matanbright/8BitComputer/pcb-files/8-Bit_Computer/8-Bit_Computer.kicad_sch

## KiCad design pcb-files/8-Bit_Computer/8-Bit_Computer.kicad_sch (2024-03-10)

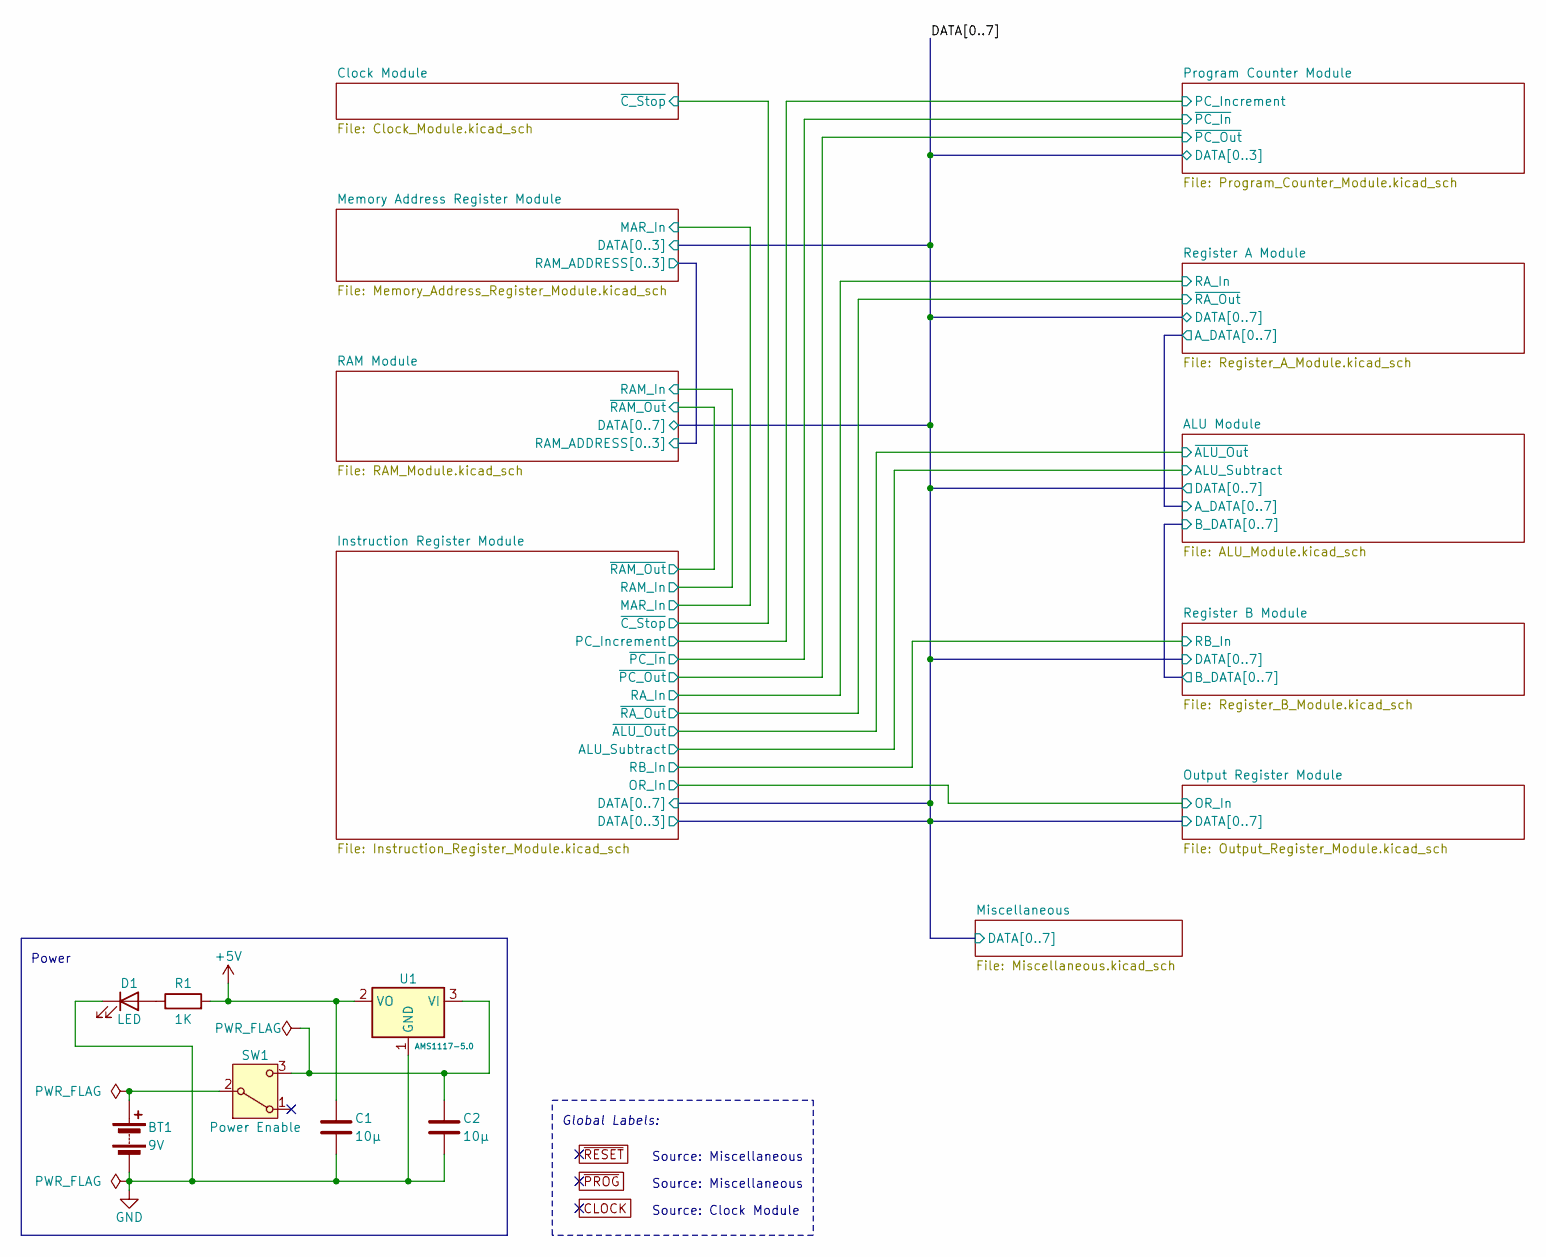
[picture p2: schematic 8-Bit_Computer.kicad_sch]

Parts:
BT1: 9V; BatteryHolder_Eagle_12BH611-GR
C1, C2: 10µ; C_Radial_D4.0mm_H7.0mm_P1.50mm
D1: LED; LED_D3.0mm
R1: 1K; R_Axial_DIN0207_L6.3mm_D2.5mm_P7.62mm_Horizontal
SW1: Power Enable; SW_SPDT
U1: AMS1117-5.0; SOT-223-3_TabPin2

Connections:
+5V: C1.1, R1.2, U1.2 (VO)
GND: BT1.2 (-), C1.2, C2.2, D1.1 (K), U1.1 (GND)
unnamed: BT1.1 (+), SW1.2 (B)
unnamed: C2.1, SW1.3 (C), U1.3 (VI)
unnamed: D1.2 (A), R1.1

Notes on the sheet:
Source: Clock Module
Power
Source: Miscellaneous
Global Labels:
