matanbright/8BitComputer/pcb-files/8-Bit_Computer/ALU_Module.kicad_sch

## KiCad design pcb-files/8-Bit_Computer/ALU_Module.kicad_sch (2024-03-10)

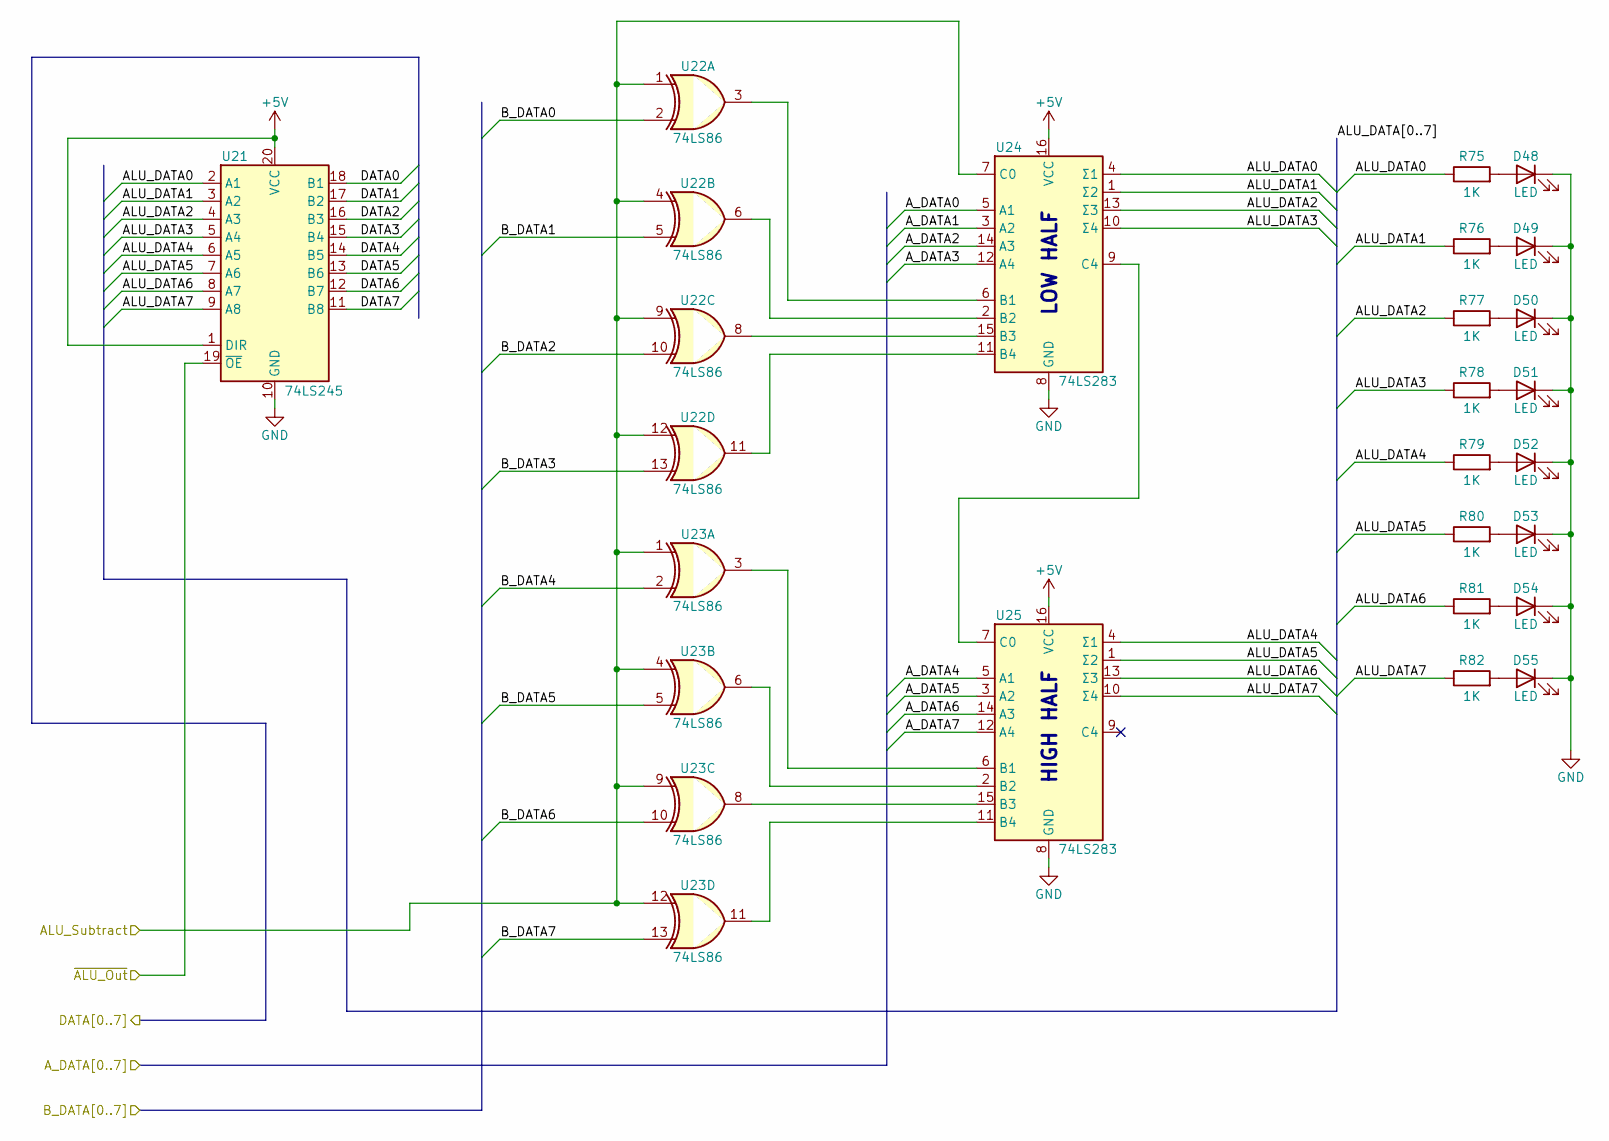
[picture p3: schematic ALU_Module.kicad_sch]

Parts:
D48, D49, D50, D51, D52, D53, D54, D55: LED; LED_D3.0mm
R75, R76, R77, R78, R79, R80, R81, R82: 1K; R_Axial_DIN0207_L6.3mm_D2.5mm_P7.62mm_Horizontal
U21: 74LS245; DIP-20_W7.62mm
U22, U23: 74LS86; DIP-14_W7.62mm
U24, U25: 74LS283; DIP-16_W7.62mm

Connections:
+5V: U21.1 (DIR), U21.20 (VCC), U24.16 (VCC), U25.16 (VCC)
ALU_DATA0: R75.1, U21.2 (A1), U24.4 (Σ1)
ALU_DATA1: R76.1, U21.3 (A2), U24.1 (Σ2)
ALU_DATA2: R77.1, U21.4 (A3), U24.13 (Σ3)
ALU_DATA3: R78.1, U21.5 (A4), U24.10 (Σ4)
ALU_DATA4: R79.1, U21.6 (A5), U25.4 (Σ1)
ALU_DATA5: R80.1, U21.7 (A6), U25.1 (Σ2)
ALU_DATA6: R81.1, U21.8 (A7), U25.13 (Σ3)
ALU_DATA7: R82.1, U21.9 (A8), U25.10 (Σ4)
ALU_Subtract: U22.1, U22.4, U22.9, U22.12, U23.1, U23.4, U23.9, U23.12, U24.7 (C0)
A_DATA0: U24.5 (A1)
A_DATA1: U24.3 (A2)
A_DATA2: U24.14 (A3)
A_DATA3: U24.12 (A4)
A_DATA4: U25.5 (A1)
A_DATA5: U25.3 (A2)
A_DATA6: U25.14 (A3)
A_DATA7: U25.12 (A4)
B_DATA0: U22.2
B_DATA1: U22.5
B_DATA2: U22.10
B_DATA3: U22.13
B_DATA4: U23.2
B_DATA5: U23.5
B_DATA6: U23.10
B_DATA7: U23.13
DATA0: U21.18 (B1)
DATA1: U21.17 (B2)
DATA2: U21.16 (B3)
DATA3: U21.15 (B4)
DATA4: U21.14 (B5)
DATA5: U21.13 (B6)
DATA6: U21.12 (B7)
DATA7: U21.11 (B8)
GND: D48.1 (K), D49.1 (K), D50.1 (K), D51.1 (K), D52.1 (K), D53.1 (K), D54.1 (K), D55.1 (K), U21.10 (GND), U24.8 (GND), U25.8 (GND)
unnamed: D48.2 (A), R75.2
unnamed: D49.2 (A), R76.2
unnamed: D50.2 (A), R77.2
unnamed: D51.2 (A), R78.2
unnamed: D52.2 (A), R79.2
unnamed: D53.2 (A), R80.2
unnamed: D54.2 (A), R81.2
unnamed: D55.2 (A), R82.2
unnamed: U22.3, U24.6 (B1)
unnamed: U22.6, U24.2 (B2)
unnamed: U22.8, U24.15 (B3)
unnamed: U22.11, U24.11 (B4)
unnamed: U23.3, U25.6 (B1)
unnamed: U23.6, U25.2 (B2)
unnamed: U23.8, U25.15 (B3)
unnamed: U23.11, U25.11 (B4)
unnamed: U24.9 (C4), U25.7 (C0)
~ALU_Out: U21.19 (~OE)

Notes on the sheet:
LOW HALF
HIGH HALF
