matanbright/8BitComputer/pcb-files/8-Bit_Computer/Clock_Module.kicad_sch

## KiCad design pcb-files/8-Bit_Computer/Clock_Module.kicad_sch (2024-03-10)

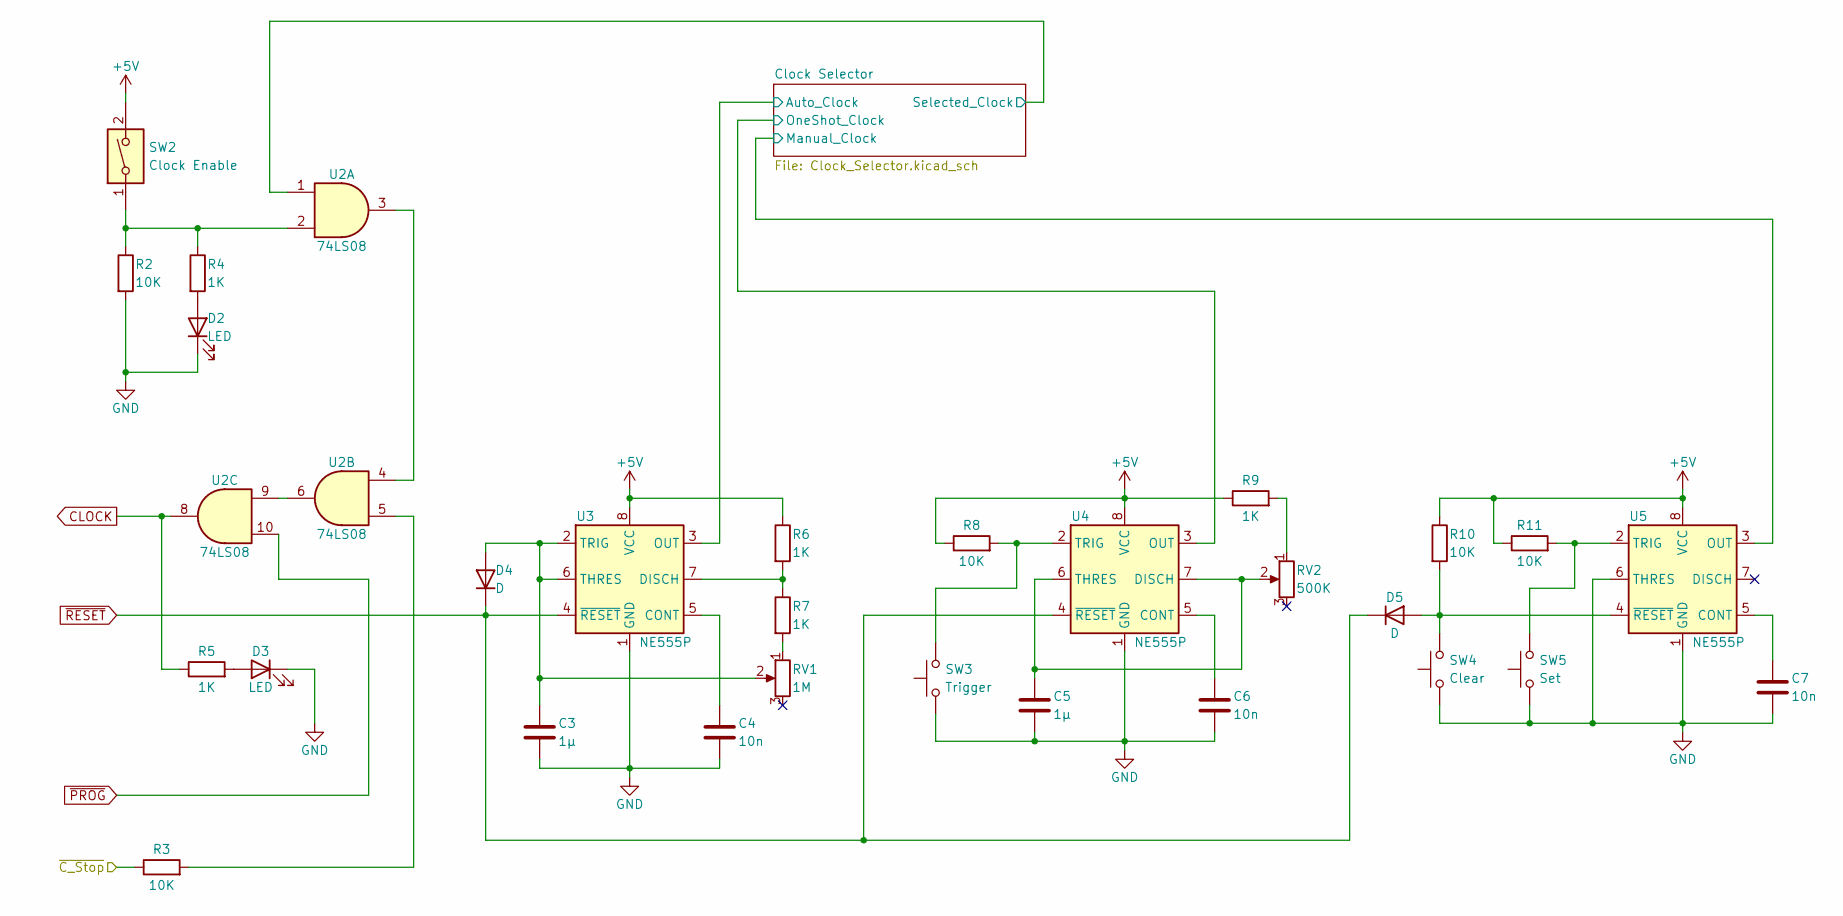
[picture p4: schematic Clock_Module.kicad_sch]

Parts:
C3, C5: 1µ; C_Disc_D5.1mm_W3.2mm_P5.00mm
C4, C6, C7: 10n; C_Disc_D5.1mm_W3.2mm_P5.00mm
D2, D3: LED; LED_D3.0mm
D4, D5: D; D_DO-34_SOD68_P7.62mm_Horizontal
R2, R3, R8, R10, R11: 10K; R_Axial_DIN0207_L6.3mm_D2.5mm_P7.62mm_Horizontal
R4, R5, R6, R7, R9: 1K; R_Axial_DIN0207_L6.3mm_D2.5mm_P7.62mm_Horizontal
RV1: 1M; Potentiometer_Vishay_T73YP_Vertical
RV2: 500K; Potentiometer_Vishay_T73YP_Vertical
SW2: Clock Enable; SW_DIP_SPSTx01_Slide_9.78x4.72mm_W7.62mm_P2.54mm
SW3: Trigger; SW_PUSH_6mm_H5mm
SW4: Clear; SW_PUSH_6mm_H5mm
SW5: Set; SW_PUSH_6mm_H5mm
U2: 74LS08; DIP-14_W7.62mm
U3, U4, U5: NE555P; DIP-8_W7.62mm

Connections:
+5V: R6.1, R8.1, R9.1, R10.1, R11.1, SW2.2, U3.8 (VCC), U4.8 (VCC), U5.8 (VCC)
Auto_Clock: U3.3 (OUT)
CLOCK: R5.1, U2.8
GND: C3.2, C4.2, C5.2, C6.2, C7.2, D2.1 (K), D3.1 (K), R2.2, SW3.1, SW4.1, SW5.1, U3.1 (GND), U4.1 (GND), U5.1 (GND), U5.6 (THRES)
Manual_Clock: U5.3 (OUT)
unnamed: C3.1, D4.2 (A), RV1.2, U3.2 (TRIG), U3.6 (THRES)
unnamed: C4.1, U3.5 (CONT)
unnamed: C5.1, RV2.2, U4.6 (THRES), U4.7 (DISCH)
unnamed: C6.1, U4.5 (CONT)
unnamed: C7.1, U5.5 (CONT)
unnamed: D2.2 (A), R4.2
unnamed: D3.2 (A), R5.2
unnamed: D5.2 (A), R10.2, SW4.2, U5.4 (~RESET)
unnamed: R2.1, R4.1, SW2.1, U2.2
unnamed: R3.2, U2.5
unnamed: R6.2, R7.1, U3.7 (DISCH)
unnamed: R7.2, RV1.1
unnamed: R8.2, SW3.2, U4.2 (TRIG)
unnamed: R9.2, RV2.1
unnamed: R11.2, SW5.2, U5.2 (TRIG)
unnamed: U2.3, U2.4
unnamed: U2.6, U2.9
OneShot_Clock: U4.3 (OUT)
Selected_Clock: U2.1
~C_Stop: R3.1
~PROG: U2.10
~RESET: D4.1 (K), D5.1 (K), U3.4 (~RESET), U4.4 (~RESET)
