matanbright/8BitComputer/pcb-files/8-Bit_Computer/Clock_Selector.kicad_sch

## KiCad design pcb-files/8-Bit_Computer/Clock_Selector.kicad_sch (2024-03-10)

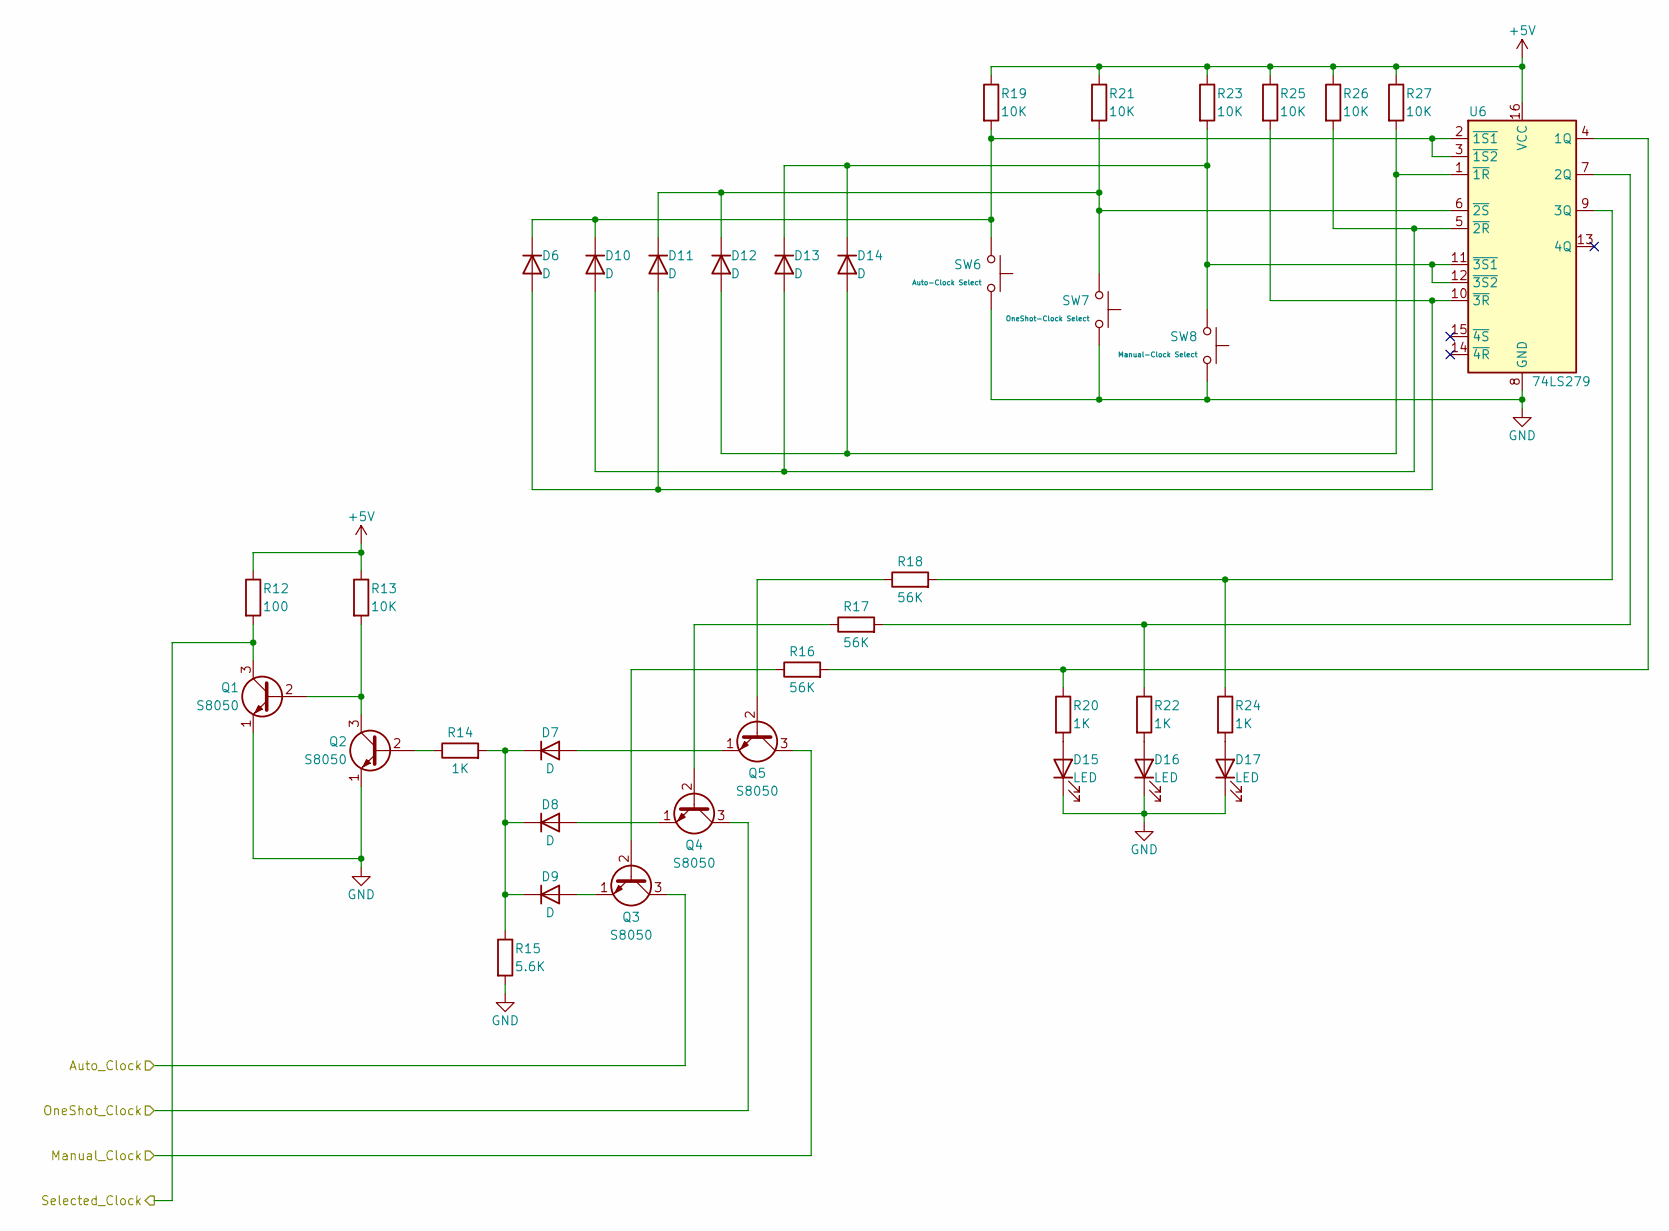
[picture p5: schematic Clock_Selector.kicad_sch]

Parts:
D6, D7, D8, D9, D10, D11, D12, D13, D14: D; D_DO-34_SOD68_P7.62mm_Horizontal
D15, D16, D17: LED; LED_D3.0mm
Q1, Q2, Q3, Q4, Q5: S8050; TO-92_Inline
R12: 100; R_Axial_DIN0207_L6.3mm_D2.5mm_P7.62mm_Horizontal
R13, R19, R21, R23, R25, R26, R27: 10K; R_Axial_DIN0207_L6.3mm_D2.5mm_P7.62mm_Horizontal
R14, R20, R22, R24: 1K; R_Axial_DIN0207_L6.3mm_D2.5mm_P7.62mm_Horizontal
R15: 5.6K; R_Axial_DIN0207_L6.3mm_D2.5mm_P7.62mm_Horizontal
R16, R17, R18: 56K; R_Axial_DIN0207_L6.3mm_D2.5mm_P7.62mm_Horizontal
SW6: Auto-Clock Select; SW_PUSH_6mm_H5mm
SW7: OneShot-Clock Select; SW_PUSH_6mm_H5mm
SW8: Manual-Clock Select; SW_PUSH_6mm_H5mm
U6: 74LS279; DIP-16_W7.62mm

Connections:
+5V: R12.1, R13.1, R19.1, R21.1, R23.1, R25.1, R26.1, R27.1, U6.16 (VCC)
Auto_Clock: Q3.3 (C)
GND: D15.1 (K), D16.1 (K), D17.1 (K), Q1.1 (E), Q2.1 (E), R15.2, SW6.1, SW7.1, SW8.1, U6.8 (GND)
Manual_Clock: Q5.3 (C)
unnamed: D7.1 (K), D8.1 (K), D9.1 (K), R14.2, R15.1
unnamed: D7.2 (A), Q5.1 (E)
unnamed: D8.2 (A), Q4.1 (E)
unnamed: D9.2 (A), Q3.1 (E)
unnamed: D6.1 (K), D10.1 (K), R19.2, SW6.2, U6.2 (~1S1), U6.3 (~1S2)
unnamed: D10.2 (A), D13.2 (A), R26.2, U6.5 (~2R)
unnamed: D11.1 (K), D12.1 (K), R21.2, SW7.2, U6.6 (~2S)
unnamed: D6.2 (A), D11.2 (A), R25.2, U6.10 (~3R)
unnamed: D12.2 (A), D14.2 (A), R27.2, U6.1 (~1R)
unnamed: D13.1 (K), D14.1 (K), R23.2, SW8.2, U6.11 (~3S1), U6.12 (~3S2)
unnamed: D15.2 (A), R20.2
unnamed: D16.2 (A), R22.2
unnamed: D17.2 (A), R24.2
unnamed: Q1.2 (B), Q2.3 (C), R13.2
unnamed: Q2.2 (B), R14.1
unnamed: Q3.2 (B), R16.1
unnamed: Q4.2 (B), R17.1
unnamed: Q5.2 (B), R18.1
unnamed: R16.2, R20.1, U6.4 (1Q)
unnamed: R17.2, R22.1, U6.7 (2Q)
unnamed: R18.2, R24.1, U6.9 (3Q)
OneShot_Clock: Q4.3 (C)
Selected_Clock: Q1.3 (C), R12.2
