matanbright/8BitComputer/pcb-files/8-Bit_Computer/Instruction_Register_Module.kicad_sch

## KiCad design pcb-files/8-Bit_Computer/Instruction_Register_Module.kicad_sch (2024-03-10)

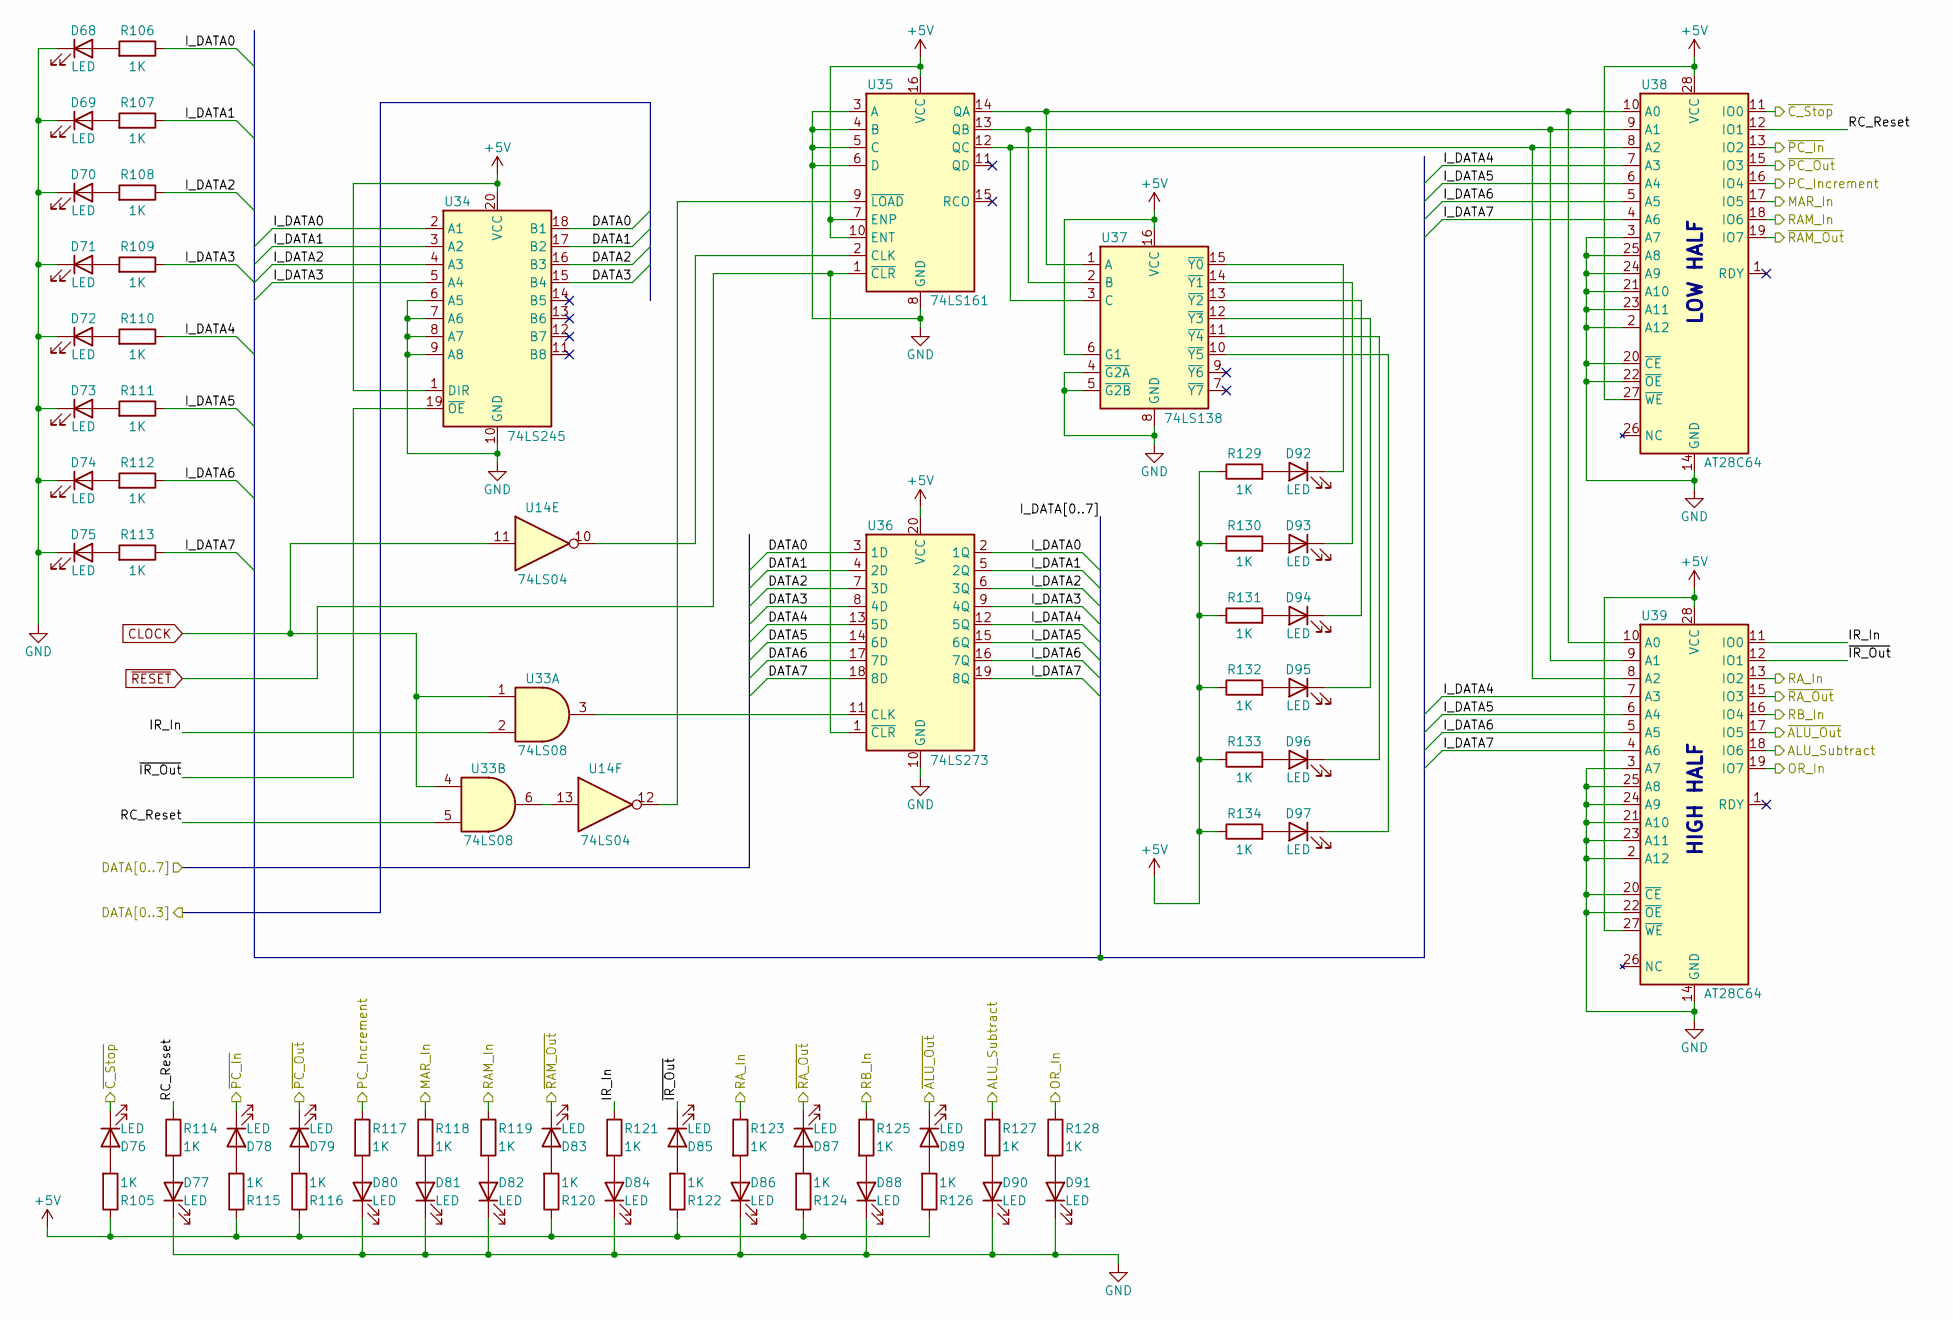
[picture p6: schematic Instruction_Register_Module.kicad_sch]

Parts:
D68, D69, D70, D71, D72, D73, D74, D75, D76, D77, D78, D79, D80, D81, D82, D83, D84, D85, D86, D87, D88, D89, D90, D91, D92, D93, D94, D95, D96, D97: LED; LED_D3.0mm
R105, R106, R107, R108, R109, R110, R111, R112, R113, R114, R115, R116, R117, R118, R119, R120, R121, R122, R123, R124, R125, R126, R127, R128, R129, R130, R131, R132, R133, R134: 1K; R_Axial_DIN0207_L6.3mm_D2.5mm_P7.62mm_Horizontal
U14: 74LS04; DIP-14_W7.62mm
U33: 74LS08; DIP-14_W7.62mm
U34: 74LS245; DIP-20_W7.62mm
U35: 74LS161; DIP-16_W7.62mm
U36: 74LS273; DIP-20_W7.62mm
U37: 74LS138; DIP-16_W7.62mm
U38, U39: AT28C64; DIP-28_W15.24mm

Connections:
+5V: R105.1, R115.1, R116.1, R120.1, R122.1, R124.1, R126.1, R129.1, R130.1, R131.1, R132.1, R133.1, R134.1, U34.1 (DIR), U34.20 (VCC), U35.7 (ENP), U35.10 (ENT), U35.16 (VCC), U36.20 (VCC), U37.6 (G1), U37.16 (VCC), U38.27 (~WE), U38.28 (VCC), U39.27 (~WE), U39.28 (VCC)
ALU_Subtract: R127.1, U39.18 (IO6)
CLOCK: U14.11, U33.1, U33.4
DATA0: U34.18 (B1), U36.3 (1D)
DATA1: U34.17 (B2), U36.4 (2D)
DATA2: U34.16 (B3), U36.7 (3D)
DATA3: U34.15 (B4), U36.8 (4D)
DATA4: U36.13 (5D)
DATA5: U36.14 (6D)
DATA6: U36.17 (7D)
DATA7: U36.18 (8D)
GND: D68.1 (K), D69.1 (K), D70.1 (K), D71.1 (K), D72.1 (K), D73.1 (K), D74.1 (K), D75.1 (K), D77.1 (K), D80.1 (K), D81.1 (K), D82.1 (K), D84.1 (K), D86.1 (K), D88.1 (K), D90.1 (K), D91.1 (K), U34.6 (A5), U34.7 (A6), U34.8 (A7), U34.9 (A8), U34.10 (GND), U35.3 (A), U35.4 (B), U35.5 (C), U35.6 (D), U35.8 (GND), U36.10 (GND), U37.4 (~G2A), U37.5 (~G2B), U37.8 (GND), U38.2 (A12), U38.3 (A7), U38.14 (GND), U38.20 (~CE), U38.21 (A10), U38.22 (~OE), U38.23 (A11), U38.24 (A9), U38.25 (A8), U39.2 (A12), U39.3 (A7), U39.14 (GND), U39.20 (~CE), U39.21 (A10), U39.22 (~OE), U39.23 (A11), U39.24 (A9), U39.25 (A8)
IR_In: R121.1, U33.2, U39.11 (IO0)
I_DATA0: R106.1, U34.2 (A1), U36.2 (1Q)
I_DATA1: R107.1, U34.3 (A2), U36.5 (2Q)
I_DATA2: R108.1, U34.4 (A3), U36.6 (3Q)
I_DATA3: R109.1, U34.5 (A4), U36.9 (4Q)
I_DATA4: R110.1, U36.12 (5Q), U38.7 (A3), U39.7 (A3)
I_DATA5: R111.1, U36.15 (6Q), U38.6 (A4), U39.6 (A4)
I_DATA6: R112.1, U36.16 (7Q), U38.5 (A5), U39.5 (A5)
I_DATA7: R113.1, U36.19 (8Q), U38.4 (A6), U39.4 (A6)
MAR_In: R118.1, U38.17 (IO5)
unnamed: D68.2 (A), R106.2
unnamed: D69.2 (A), R107.2
unnamed: D70.2 (A), R108.2
unnamed: D71.2 (A), R109.2
unnamed: D72.2 (A), R110.2
unnamed: D73.2 (A), R111.2
unnamed: D74.2 (A), R112.2
unnamed: D75.2 (A), R113.2
unnamed: D76.2 (A), R105.2
unnamed: D77.2 (A), R114.2
unnamed: D78.2 (A), R115.2
unnamed: D79.2 (A), R116.2
unnamed: D80.2 (A), R117.2
unnamed: D81.2 (A), R118.2
unnamed: D82.2 (A), R119.2
unnamed: D83.2 (A), R120.2
unnamed: D84.2 (A), R121.2
unnamed: D85.2 (A), R122.2
unnamed: D86.2 (A), R123.2
unnamed: D87.2 (A), R124.2
unnamed: D88.2 (A), R125.2
unnamed: D89.2 (A), R126.2
unnamed: D90.2 (A), R127.2
unnamed: D91.2 (A), R128.2
unnamed: D92.1 (K), U37.15 (~Y0)
unnamed: D92.2 (A), R129.2
unnamed: D93.1 (K), U37.14 (~Y1)
unnamed: D93.2 (A), R130.2
unnamed: D94.1 (K), U37.13 (~Y2)
unnamed: D94.2 (A), R131.2
unnamed: D95.1 (K), U37.12 (~Y3)
unnamed: D95.2 (A), R132.2
unnamed: D96.1 (K), U37.11 (~Y4)
unnamed: D96.2 (A), R133.2
unnamed: D97.1 (K), U37.10 (~Y5)
unnamed: D97.2 (A), R134.2
unnamed: U14.10, U35.2 (CLK)
unnamed: U14.12, U35.9 (~LOAD)
unnamed: U14.13, U33.6
unnamed: U33.3, U36.11 (CLK)
unnamed: U35.12 (QC), U37.3 (C), U38.8 (A2), U39.8 (A2)
unnamed: U35.13 (QB), U37.2 (B), U38.9 (A1), U39.9 (A1)
unnamed: U35.14 (QA), U37.1 (A), U38.10 (A0), U39.10 (A0)
OR_In: R128.1, U39.19 (IO7)
PC_Increment: R117.1, U38.16 (IO4)
RAM_In: R119.1, U38.18 (IO6)
RA_In: R123.1, U39.13 (IO2)
RB_In: R125.1, U39.16 (IO4)
RC_Reset: R114.1, U33.5, U38.12 (IO1)
~ALU_Out: D89.1 (K), U39.17 (IO5)
~C_Stop: D76.1 (K), U38.11 (IO0)
~IR_Out: D85.1 (K), U34.19 (~OE), U39.12 (IO1)
~PC_In: D78.1 (K), U38.13 (IO2)
~PC_Out: D79.1 (K), U38.15 (IO3)
~RAM_Out: D83.1 (K), U38.19 (IO7)
~RA_Out: D87.1 (K), U39.15 (IO3)
~RESET: U35.1 (~CLR), U36.1 (~CLR)

Notes on the sheet:
HIGH HALF
LOW HALF
