matanbright/8BitComputer/pcb-files/8-Bit_Computer/Memory_Address_Overrider.kicad_sch

## KiCad design pcb-files/8-Bit_Computer/Memory_Address_Overrider.kicad_sch (2024-03-10)

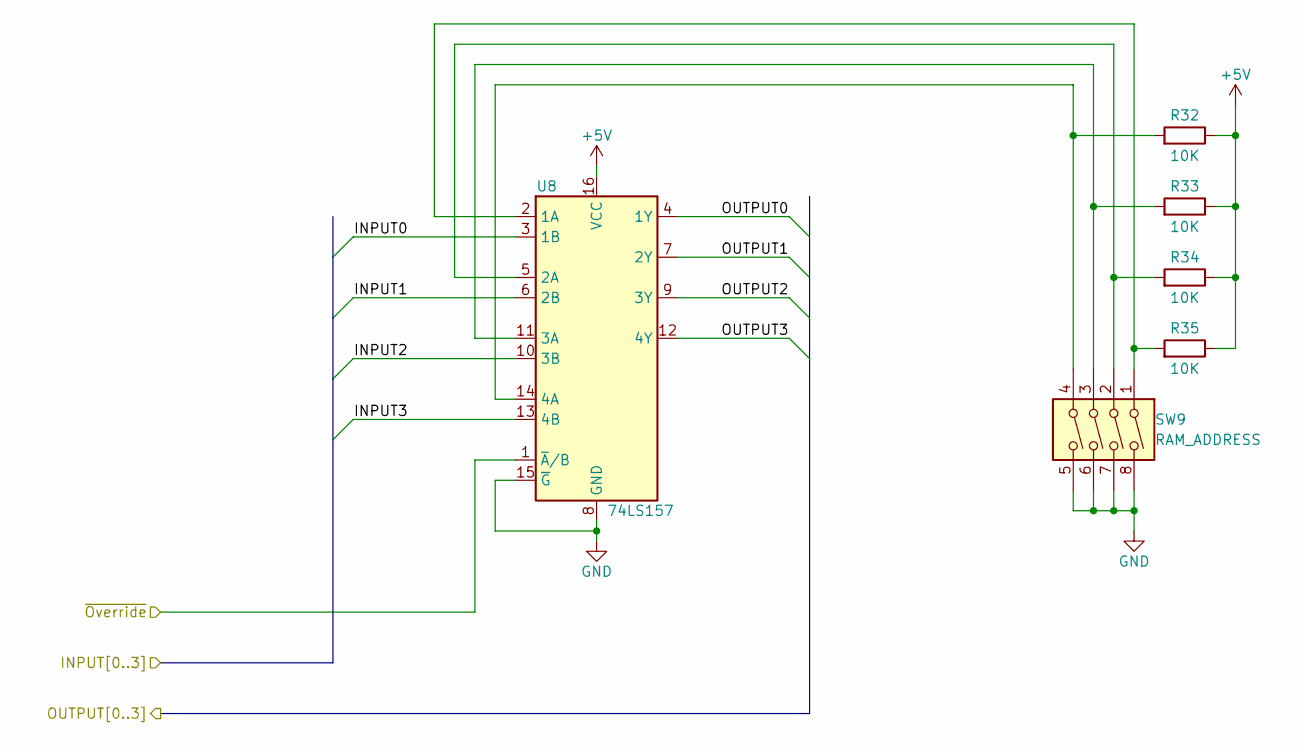
[picture p7: schematic Memory_Address_Overrider.kicad_sch]

Parts:
R32, R33, R34, R35: 10K; R_Axial_DIN0207_L6.3mm_D2.5mm_P7.62mm_Horizontal
SW9: RAM_ADDRESS; SW_DIP_SPSTx04_Slide_9.78x12.34mm_W7.62mm_P2.54mm
U8: 74LS157; DIP-16_W7.62mm

Connections:
+5V: R32.1, R33.1, R34.1, R35.1, U8.16 (VCC)
GND: SW9.5, SW9.6, SW9.7, SW9.8, U8.8 (GND), U8.15 (~G)
INPUT0: U8.3 (1B)
INPUT1: U8.6 (2B)
INPUT2: U8.10 (3B)
INPUT3: U8.13 (4B)
unnamed: R32.2, SW9.4, U8.14 (4A)
unnamed: R33.2, SW9.3, U8.11 (3A)
unnamed: R34.2, SW9.2, U8.5 (2A)
unnamed: R35.2, SW9.1, U8.2 (1A)
OUTPUT0: U8.4 (1Y)
OUTPUT1: U8.7 (2Y)
OUTPUT2: U8.9 (3Y)
OUTPUT3: U8.12 (4Y)
~Override: U8.1 (~A/B)
