matanbright/8BitComputer/pcb-files/8-Bit_Computer/Memory_Address_Register_Module.kicad_sch

## KiCad design pcb-files/8-Bit_Computer/Memory_Address_Register_Module.kicad_sch (2024-03-10)

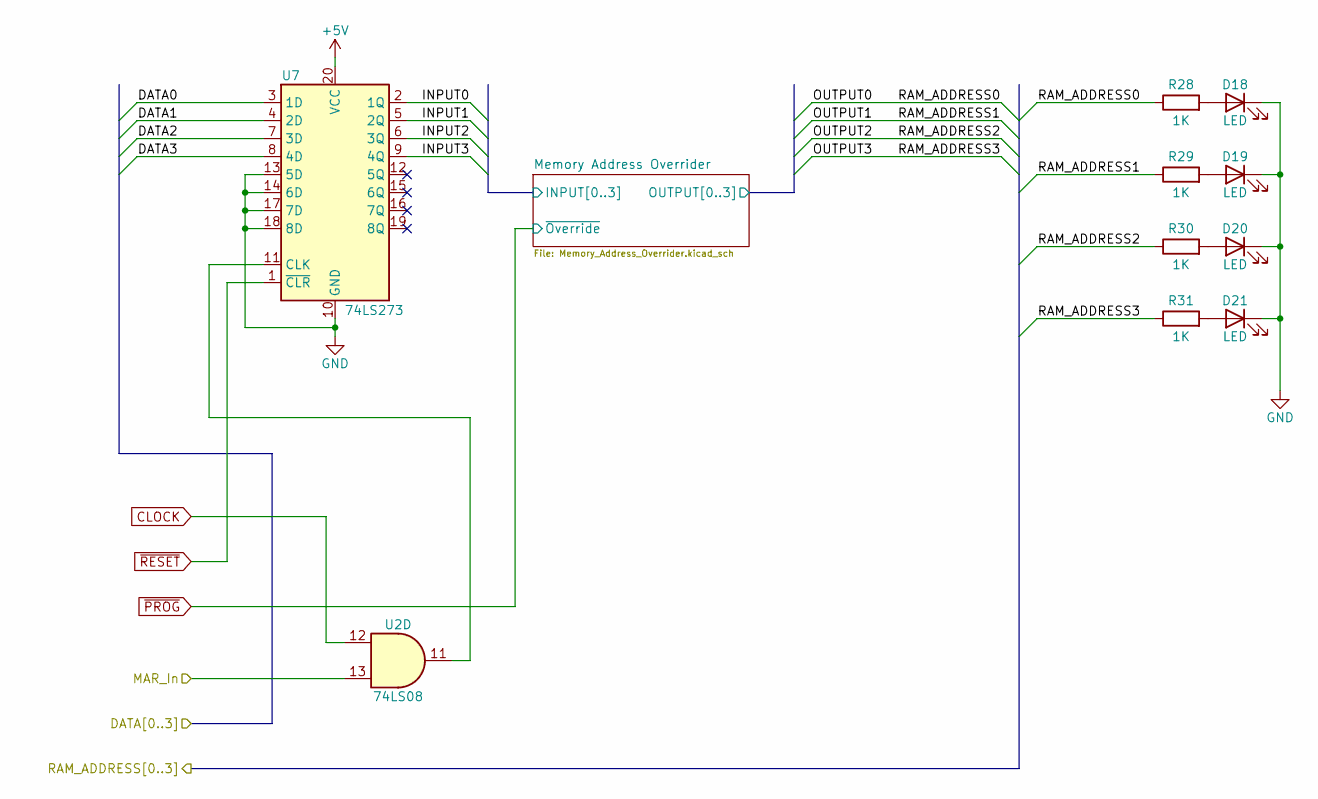
[picture p8: schematic Memory_Address_Register_Module.kicad_sch]

Parts:
D18, D19, D20, D21: LED; LED_D3.0mm
R28, R29, R30, R31: 1K; R_Axial_DIN0207_L6.3mm_D2.5mm_P7.62mm_Horizontal
U2: 74LS08; DIP-14_W7.62mm
U7: 74LS273; DIP-20_W7.62mm

Connections:
+5V: U7.20 (VCC)
CLOCK: U2.12
DATA0: U7.3 (1D)
DATA1: U7.4 (2D)
DATA2: U7.7 (3D)
DATA3: U7.8 (4D)
GND: D18.1 (K), D19.1 (K), D20.1 (K), D21.1 (K), U7.10 (GND), U7.13 (5D), U7.14 (6D), U7.17 (7D), U7.18 (8D)
INPUT0: U7.2 (1Q)
INPUT1: U7.5 (2Q)
INPUT2: U7.6 (3Q)
INPUT3: U7.9 (4Q)
MAR_In: U2.13
unnamed: D18.2 (A), R28.2
unnamed: D19.2 (A), R29.2
unnamed: D20.2 (A), R30.2
unnamed: D21.2 (A), R31.2
unnamed: U2.11, U7.11 (CLK)
OUTPUT0: R28.1
OUTPUT1: R29.1
OUTPUT2: R30.1
OUTPUT3: R31.1
~RESET: U7.1 (~CLR)
