matanbright/8BitComputer/pcb-files/8-Bit_Computer/Memory_Data_Overrider.kicad_sch

## KiCad design pcb-files/8-Bit_Computer/Memory_Data_Overrider.kicad_sch (2024-03-10)

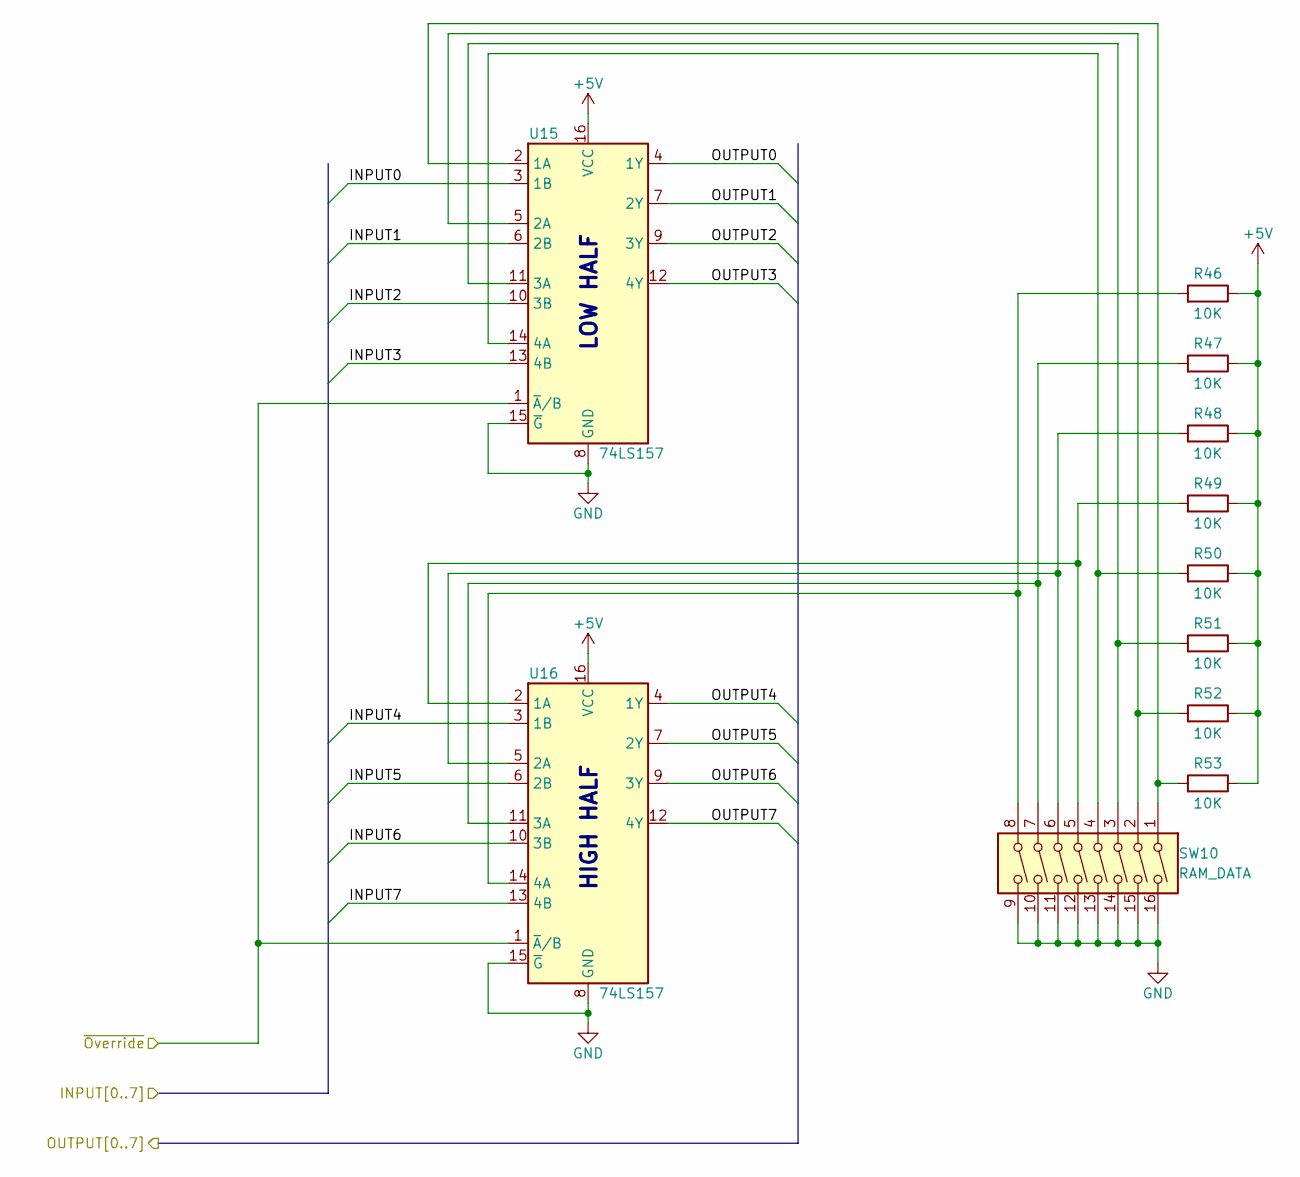
[picture p9: schematic Memory_Data_Overrider.kicad_sch]

Parts:
R46, R47, R48, R49, R50, R51, R52, R53: 10K; R_Axial_DIN0207_L6.3mm_D2.5mm_P7.62mm_Horizontal
SW10: RAM_DATA; SW_DIP_SPSTx08_Slide_9.78x22.5mm_W7.62mm_P2.54mm
U15, U16: 74LS157; DIP-16_W7.62mm

Connections:
+5V: R46.1, R47.1, R48.1, R49.1, R50.1, R51.1, R52.1, R53.1, U15.16 (VCC), U16.16 (VCC)
GND: SW10.9, SW10.10, SW10.11, SW10.12, SW10.13, SW10.14, SW10.15, SW10.16, U15.8 (GND), U15.15 (~G), U16.8 (GND), U16.15 (~G)
INPUT0: U15.3 (1B)
INPUT1: U15.6 (2B)
INPUT2: U15.10 (3B)
INPUT3: U15.13 (4B)
INPUT4: U16.3 (1B)
INPUT5: U16.6 (2B)
INPUT6: U16.10 (3B)
INPUT7: U16.13 (4B)
unnamed: R46.2, SW10.8, U16.14 (4A)
unnamed: R47.2, SW10.7, U16.11 (3A)
unnamed: R48.2, SW10.6, U16.5 (2A)
unnamed: R49.2, SW10.5, U16.2 (1A)
unnamed: R50.2, SW10.4, U15.14 (4A)
unnamed: R51.2, SW10.3, U15.11 (3A)
unnamed: R52.2, SW10.2, U15.5 (2A)
unnamed: R53.2, SW10.1, U15.2 (1A)
OUTPUT0: U15.4 (1Y)
OUTPUT1: U15.7 (2Y)
OUTPUT2: U15.9 (3Y)
OUTPUT3: U15.12 (4Y)
OUTPUT4: U16.4 (1Y)
OUTPUT5: U16.7 (2Y)
OUTPUT6: U16.9 (3Y)
OUTPUT7: U16.12 (4Y)
~Override: U15.1 (~A/B), U16.1 (~A/B)

Notes on the sheet:
LOW HALF
HIGH HALF
