matanbright/8BitComputer/pcb-files/8-Bit_Computer/Memory_Write_Overrider.kicad_sch

## KiCad design pcb-files/8-Bit_Computer/Memory_Write_Overrider.kicad_sch (2024-03-10)

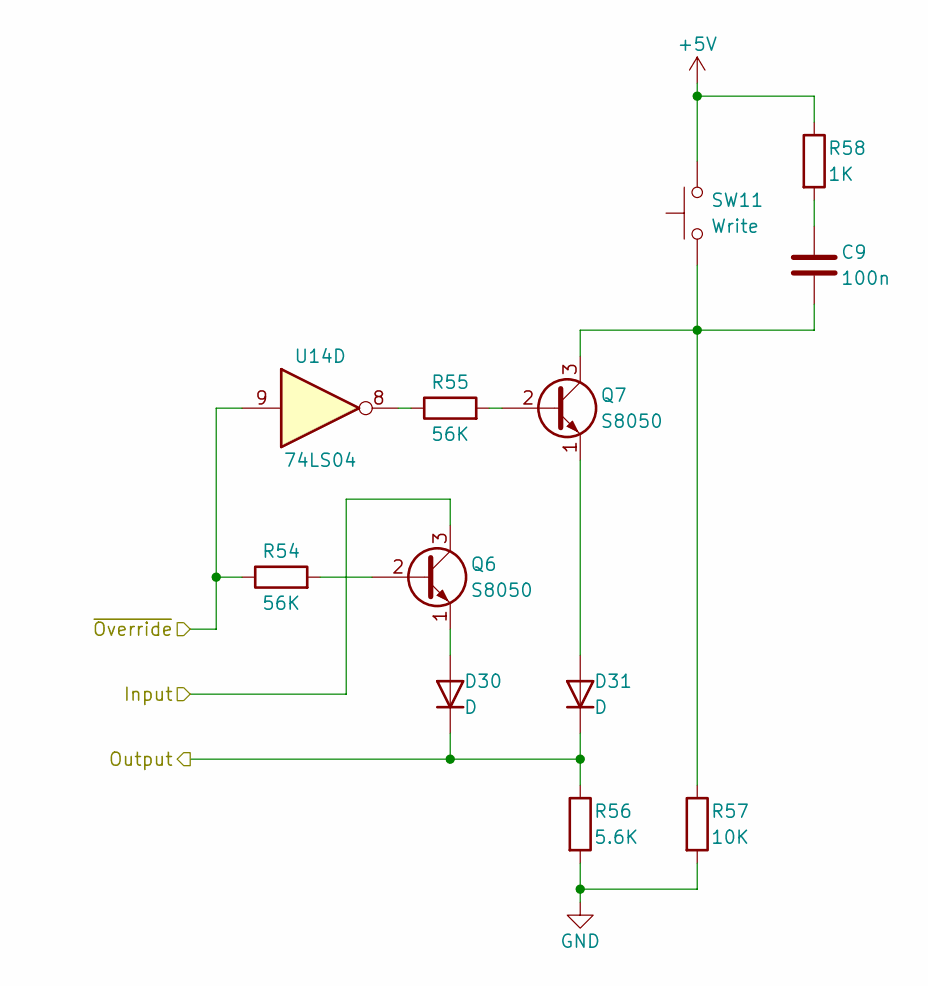
[picture p10: schematic Memory_Write_Overrider.kicad_sch]

Parts:
C9: 100n; C_Disc_D5.1mm_W3.2mm_P5.00mm
D30, D31: D; D_DO-34_SOD68_P7.62mm_Horizontal
Q6, Q7: S8050; TO-92_Inline
R54, R55: 56K; R_Axial_DIN0207_L6.3mm_D2.5mm_P7.62mm_Horizontal
R56: 5.6K; R_Axial_DIN0207_L6.3mm_D2.5mm_P7.62mm_Horizontal
R57: 10K; R_Axial_DIN0207_L6.3mm_D2.5mm_P7.62mm_Horizontal
R58: 1K; R_Axial_DIN0207_L6.3mm_D2.5mm_P7.62mm_Horizontal
SW11: Write; SW_PUSH_6mm_H5mm
U14: 74LS04; DIP-14_W7.62mm

Connections:
+5V: R58.1, SW11.2
GND: R56.2, R57.2
Input: Q6.3 (C)
unnamed: C9.1, R58.2
unnamed: C9.2, Q7.3 (C), R57.1, SW11.1
unnamed: D30.2 (A), Q6.1 (E)
unnamed: D31.2 (A), Q7.1 (E)
unnamed: Q6.2 (B), R54.2
unnamed: Q7.2 (B), R55.2
unnamed: R55.1, U14.8
Output: D30.1 (K), D31.1 (K), R56.1
~Override: R54.1, U14.9
