matanbright/8BitComputer/pcb-files/8-Bit_Computer/Miscellaneous.kicad_sch

## KiCad design pcb-files/8-Bit_Computer/Miscellaneous.kicad_sch (2024-03-10)

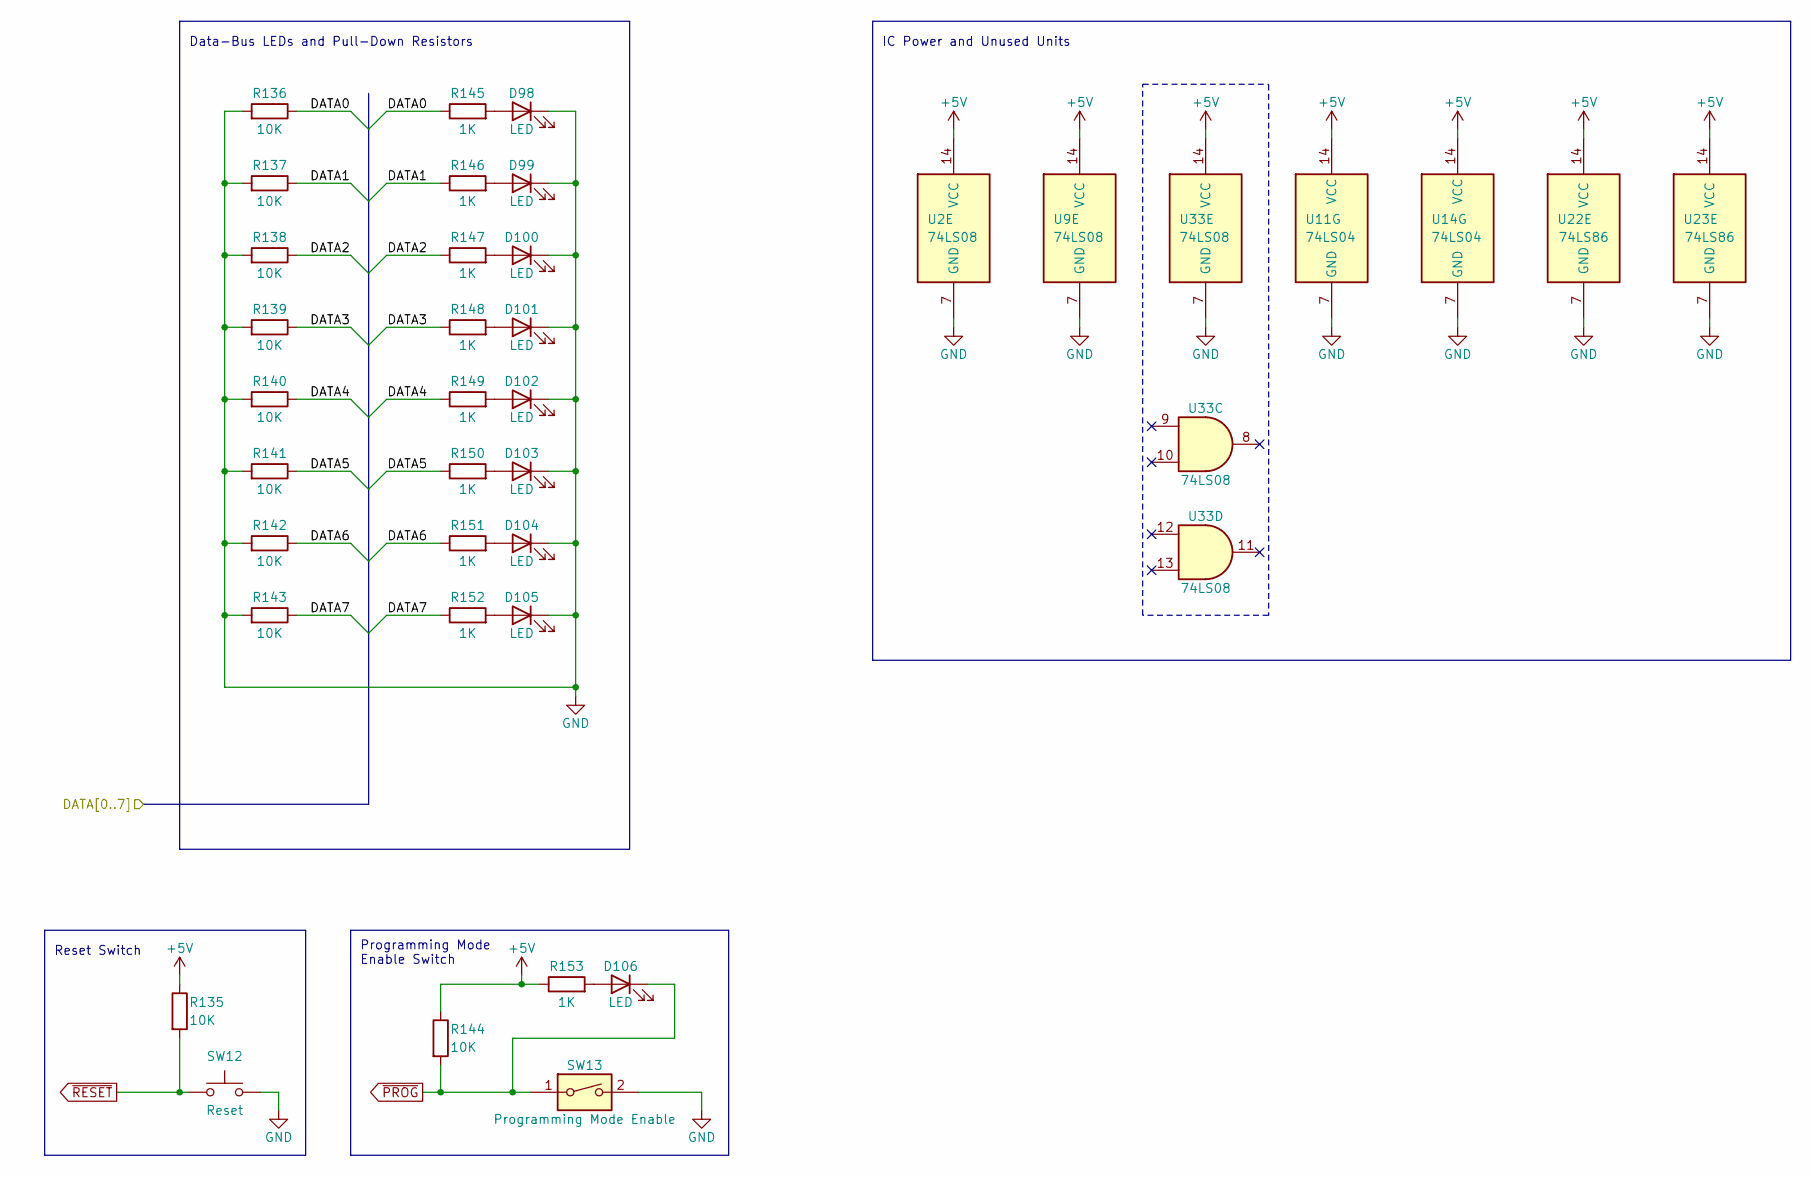
[picture p11: schematic Miscellaneous.kicad_sch]

Parts:
D98, D99, D100, D101, D102, D103, D104, D105, D106: LED; LED_D3.0mm
R135, R136, R137, R138, R139, R140, R141, R142, R143, R144: 10K; R_Axial_DIN0207_L6.3mm_D2.5mm_P7.62mm_Horizontal
R145, R146, R147, R148, R149, R150, R151, R152, R153: 1K; R_Axial_DIN0207_L6.3mm_D2.5mm_P7.62mm_Horizontal
SW12: Reset; SW_PUSH_6mm_H5mm
SW13: Programming Mode Enable; SW_DIP_SPSTx01_Slide_9.78x4.72mm_W7.62mm_P2.54mm
U2, U9, U33: 74LS08; DIP-14_W7.62mm
U11, U14: 74LS04; DIP-14_W7.62mm
U22, U23: 74LS86; DIP-14_W7.62mm

Connections:
+5V: R135.1, R144.1, R153.1, U2.14 (VCC), U9.14 (VCC), U11.14 (VCC), U14.14 (VCC), U22.14 (VCC), U23.14 (VCC), U33.14 (VCC)
DATA0: R136.1, R145.1
DATA1: R137.1, R146.1
DATA2: R138.1, R147.1
DATA3: R139.1, R148.1
DATA4: R140.1, R149.1
DATA5: R141.1, R150.1
DATA6: R142.1, R151.1
DATA7: R143.1, R152.1
GND: D98.1 (K), D99.1 (K), D100.1 (K), D101.1 (K), D102.1 (K), D103.1 (K), D104.1 (K), D105.1 (K), R136.2, R137.2, R138.2, R139.2, R140.2, R141.2, R142.2, R143.2, SW12.2, SW13.2, U2.7 (GND), U9.7 (GND), U11.7 (GND), U14.7 (GND), U22.7 (GND), U23.7 (GND), U33.7 (GND)
unnamed: D98.2 (A), R145.2
unnamed: D99.2 (A), R146.2
unnamed: D100.2 (A), R147.2
unnamed: D101.2 (A), R148.2
unnamed: D102.2 (A), R149.2
unnamed: D103.2 (A), R150.2
unnamed: D104.2 (A), R151.2
unnamed: D105.2 (A), R152.2
unnamed: D106.2 (A), R153.2
~PROG: D106.1 (K), R144.2, SW13.1
~RESET: R135.2, SW12.1

Notes on the sheet:
IC Power and Unused Units
Reset Switch
Data-Bus LEDs and Pull-Down Resistors
Programming Mode Enable Switch
