matanbright/8BitComputer/pcb-files/8-Bit_Computer/Output_Register_Module.kicad_sch

## KiCad design pcb-files/8-Bit_Computer/Output_Register_Module.kicad_sch (2024-03-10)

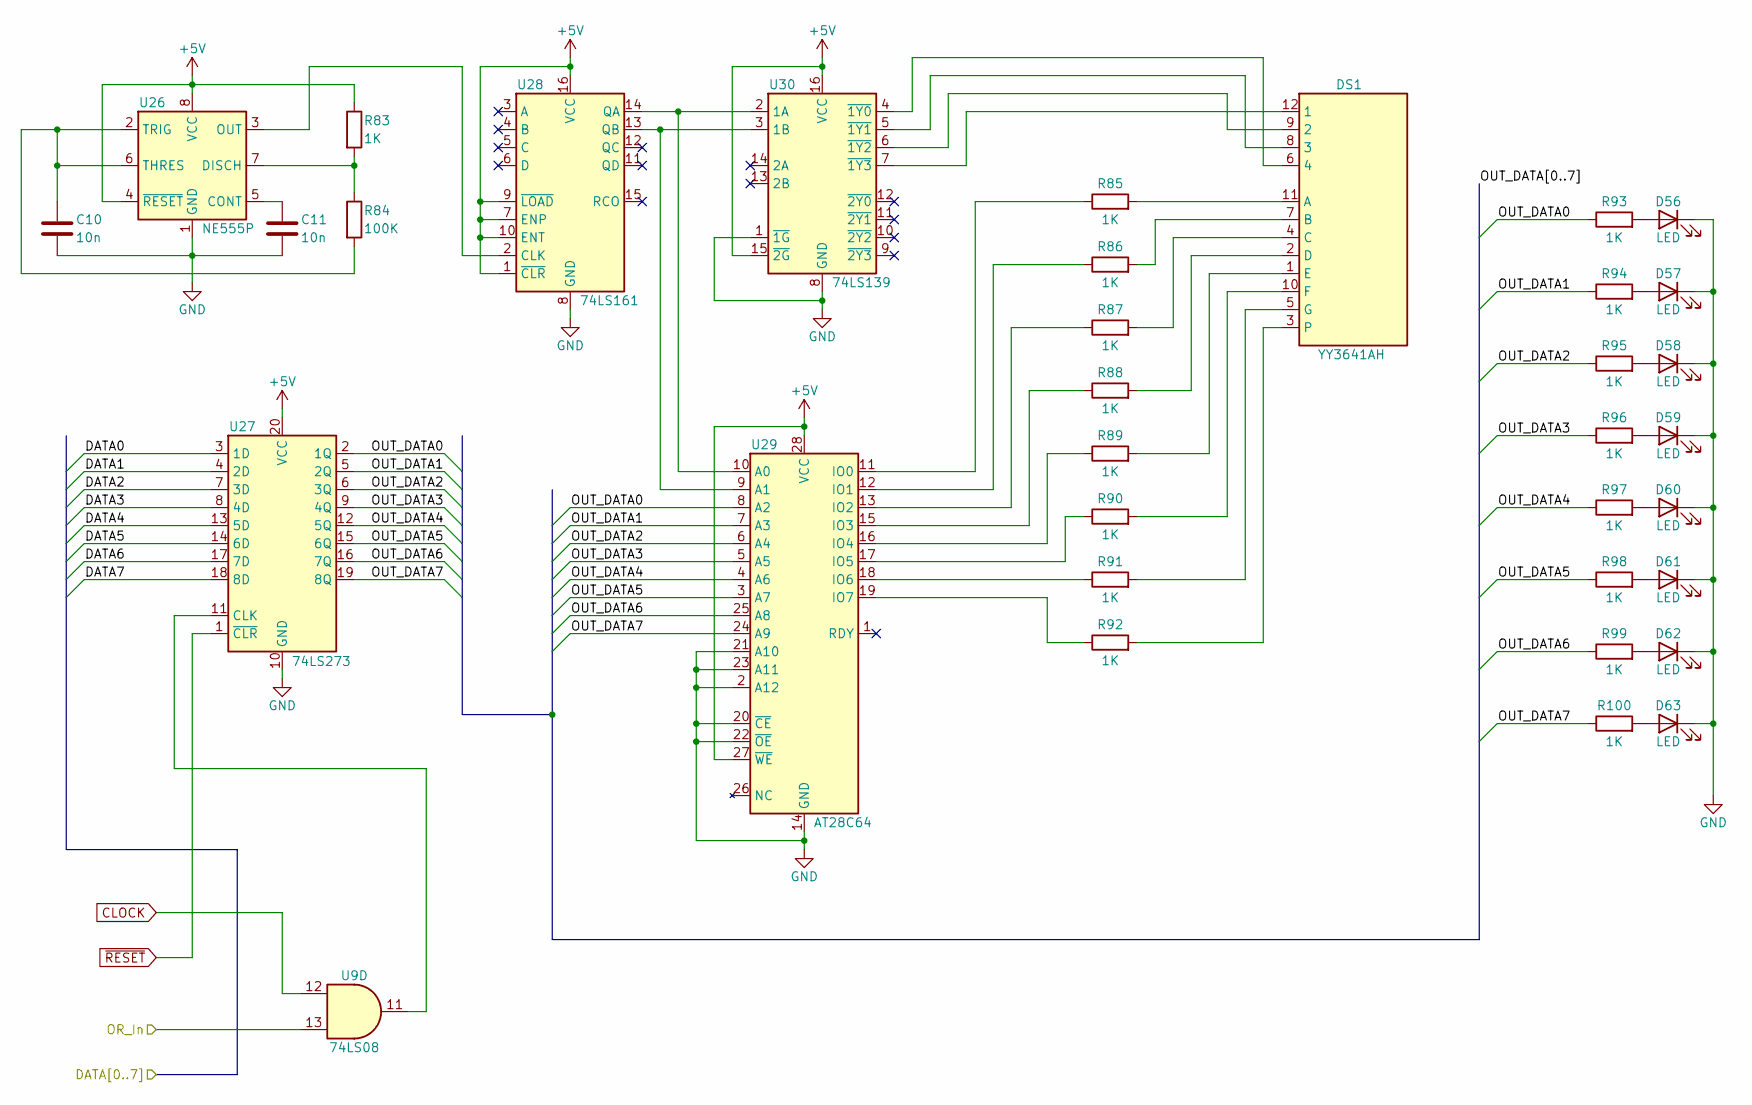
[picture p12: schematic Output_Register_Module.kicad_sch]

Parts:
C10, C11: 10n; C_Disc_D5.1mm_W3.2mm_P5.00mm
D56, D57, D58, D59, D60, D61, D62, D63: LED; LED_D3.0mm
DS1: YY3641AH
R83, R85, R86, R87, R88, R89, R90, R91, R92, R93, R94, R95, R96, R97, R98, R99, R100: 1K; R_Axial_DIN0207_L6.3mm_D2.5mm_P7.62mm_Horizontal
R84: 100K; R_Axial_DIN0207_L6.3mm_D2.5mm_P7.62mm_Horizontal
U9: 74LS08; DIP-14_W7.62mm
U26: NE555P; DIP-8_W7.62mm
U27: 74LS273; DIP-20_W7.62mm
U28: 74LS161; DIP-16_W7.62mm
U29: AT28C64; DIP-28_W15.24mm
U30: 74LS139; DIP-16_W7.62mm

Connections:
+5V: R83.1, U26.4 (~RESET), U26.8 (VCC), U27.20 (VCC), U28.1 (~CLR), U28.7 (ENP), U28.9 (~LOAD), U28.10 (ENT), U28.16 (VCC), U29.27 (~WE), U29.28 (VCC), U30.15 (~2G), U30.16 (VCC)
CLOCK: U9.12
DATA0: U27.3 (1D)
DATA1: U27.4 (2D)
DATA2: U27.7 (3D)
DATA3: U27.8 (4D)
DATA4: U27.13 (5D)
DATA5: U27.14 (6D)
DATA6: U27.17 (7D)
DATA7: U27.18 (8D)
GND: C10.2, C11.2, D56.1 (K), D57.1 (K), D58.1 (K), D59.1 (K), D60.1 (K), D61.1 (K), D62.1 (K), D63.1 (K), U26.1 (GND), U27.10 (GND), U28.8 (GND), U29.2 (A12), U29.14 (GND), U29.20 (~CE), U29.21 (A10), U29.22 (~OE), U29.23 (A11), U30.1 (~1G), U30.8 (GND)
unnamed: C10.1, R84.2, U26.2 (TRIG), U26.6 (THRES)
unnamed: C11.1, U26.5 (CONT)
unnamed: D56.2 (A), R93.2
unnamed: D57.2 (A), R94.2
unnamed: D58.2 (A), R95.2
unnamed: D59.2 (A), R96.2
unnamed: D60.2 (A), R97.2
unnamed: D61.2 (A), R98.2
unnamed: D62.2 (A), R99.2
unnamed: D63.2 (A), R100.2
unnamed: DS1.1 (E), R89.2
unnamed: DS1.2 (D), R88.2
unnamed: DS1.3, R92.2
unnamed: DS1.4 (C), R87.2
unnamed: DS1.5 (G), R91.2
unnamed: DS1.6 (4), U30.4 (~1Y0)
unnamed: DS1.7 (B), R86.2
unnamed: DS1.8 (3), U30.5 (~1Y1)
unnamed: DS1.9 (2), U30.6 (~1Y2)
unnamed: DS1.10 (F), R90.2
unnamed: DS1.11 (A), R85.2
unnamed: DS1.12 (1), U30.7 (~1Y3)
unnamed: R83.2, R84.1, U26.7 (DISCH)
unnamed: R85.1, U29.11 (IO0)
unnamed: R86.1, U29.12 (IO1)
unnamed: R87.1, U29.13 (IO2)
unnamed: R88.1, U29.15 (IO3)
unnamed: R89.1, U29.16 (IO4)
unnamed: R90.1, U29.17 (IO5)
unnamed: R91.1, U29.18 (IO6)
unnamed: R92.1, U29.19 (IO7)
unnamed: U26.3 (OUT), U28.2 (CLK)
unnamed: U9.11, U27.11 (CLK)
unnamed: U28.13 (QB), U29.9 (A1), U30.3 (1B)
unnamed: U28.14 (QA), U29.10 (A0), U30.2 (1A)
OR_In: U9.13
OUT_DATA0: R93.1, U27.2 (1Q), U29.8 (A2)
OUT_DATA1: R94.1, U27.5 (2Q), U29.7 (A3)
OUT_DATA2: R95.1, U27.6 (3Q), U29.6 (A4)
OUT_DATA3: R96.1, U27.9 (4Q), U29.5 (A5)
OUT_DATA4: R97.1, U27.12 (5Q), U29.4 (A6)
OUT_DATA5: R98.1, U27.15 (6Q), U29.3 (A7)
OUT_DATA6: R99.1, U27.16 (7Q), U29.25 (A8)
OUT_DATA7: R100.1, U27.19 (8Q), U29.24 (A9)
~RESET: U27.1 (~CLR)
