matanbright/8BitComputer/pcb-files/8-Bit_Computer/Program_Counter_Module.kicad_sch

## KiCad design pcb-files/8-Bit_Computer/Program_Counter_Module.kicad_sch (2024-03-10)

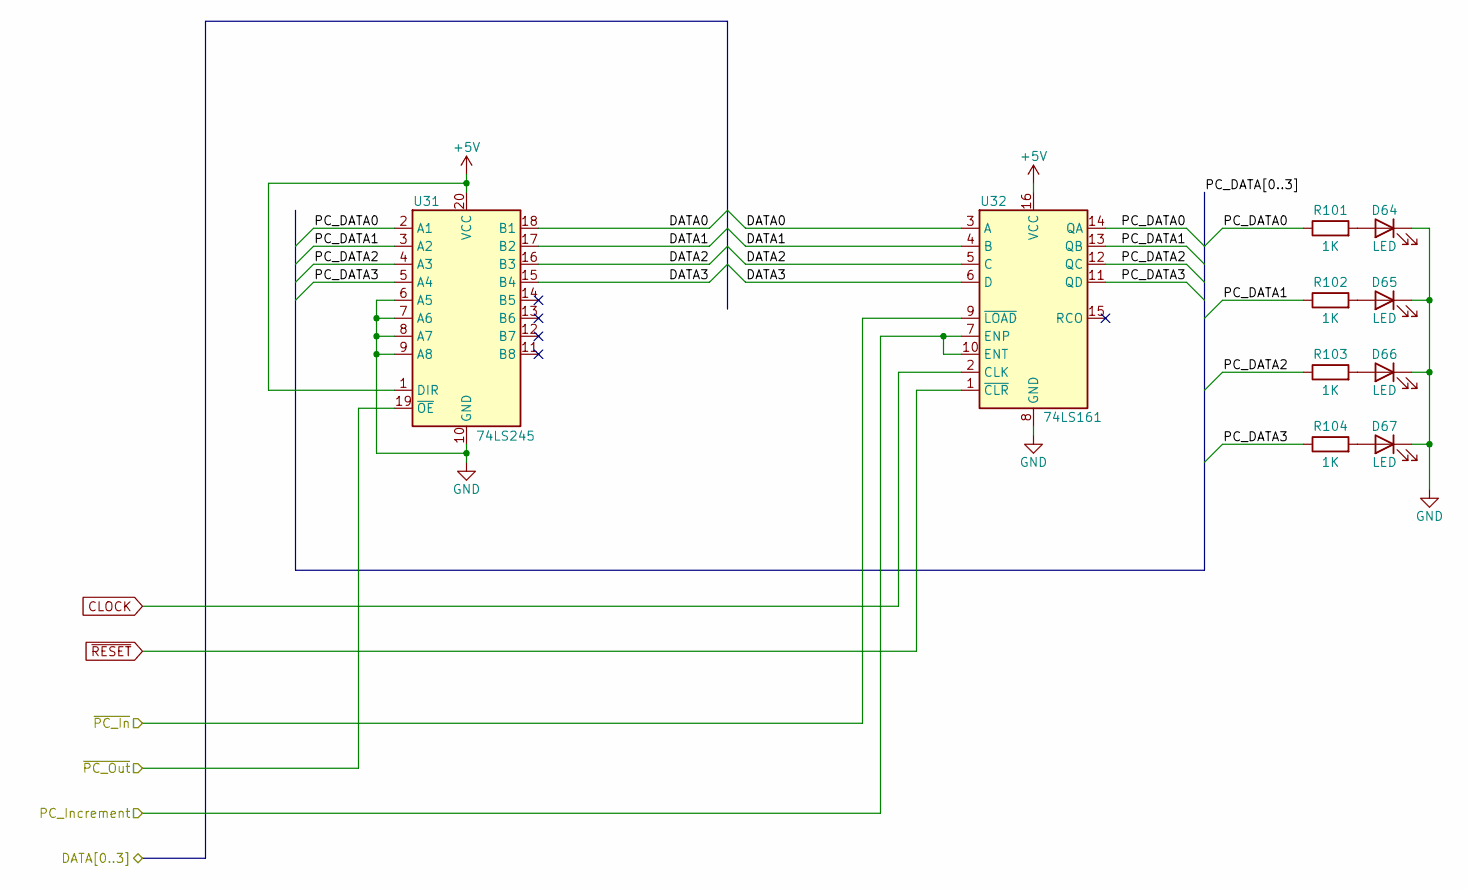
[picture p13: schematic Program_Counter_Module.kicad_sch]

Parts:
D64, D65, D66, D67: LED; LED_D3.0mm
R101, R102, R103, R104: 1K; R_Axial_DIN0207_L6.3mm_D2.5mm_P7.62mm_Horizontal
U31: 74LS245; DIP-20_W7.62mm
U32: 74LS161; DIP-16_W7.62mm

Connections:
+5V: U31.1 (DIR), U31.20 (VCC), U32.16 (VCC)
CLOCK: U32.2 (CLK)
DATA0: U31.18 (B1), U32.3 (A)
DATA1: U31.17 (B2), U32.4 (B)
DATA2: U31.16 (B3), U32.5 (C)
DATA3: U31.15 (B4), U32.6 (D)
GND: D64.1 (K), D65.1 (K), D66.1 (K), D67.1 (K), U31.6 (A5), U31.7 (A6), U31.8 (A7), U31.9 (A8), U31.10 (GND), U32.8 (GND)
unnamed: D64.2 (A), R101.2
unnamed: D65.2 (A), R102.2
unnamed: D66.2 (A), R103.2
unnamed: D67.2 (A), R104.2
PC_DATA0: R101.1, U31.2 (A1), U32.14 (QA)
PC_DATA1: R102.1, U31.3 (A2), U32.13 (QB)
PC_DATA2: R103.1, U31.4 (A3), U32.12 (QC)
PC_DATA3: R104.1, U31.5 (A4), U32.11 (QD)
PC_Increment: U32.7 (ENP), U32.10 (ENT)
~PC_In: U32.9 (~LOAD)
~PC_Out: U31.19 (~OE)
~RESET: U32.1 (~CLR)
