matanbright/8BitComputer/pcb-files/8-Bit_Computer/RAM_Module.kicad_sch

## KiCad design pcb-files/8-Bit_Computer/RAM_Module.kicad_sch (2024-03-10)

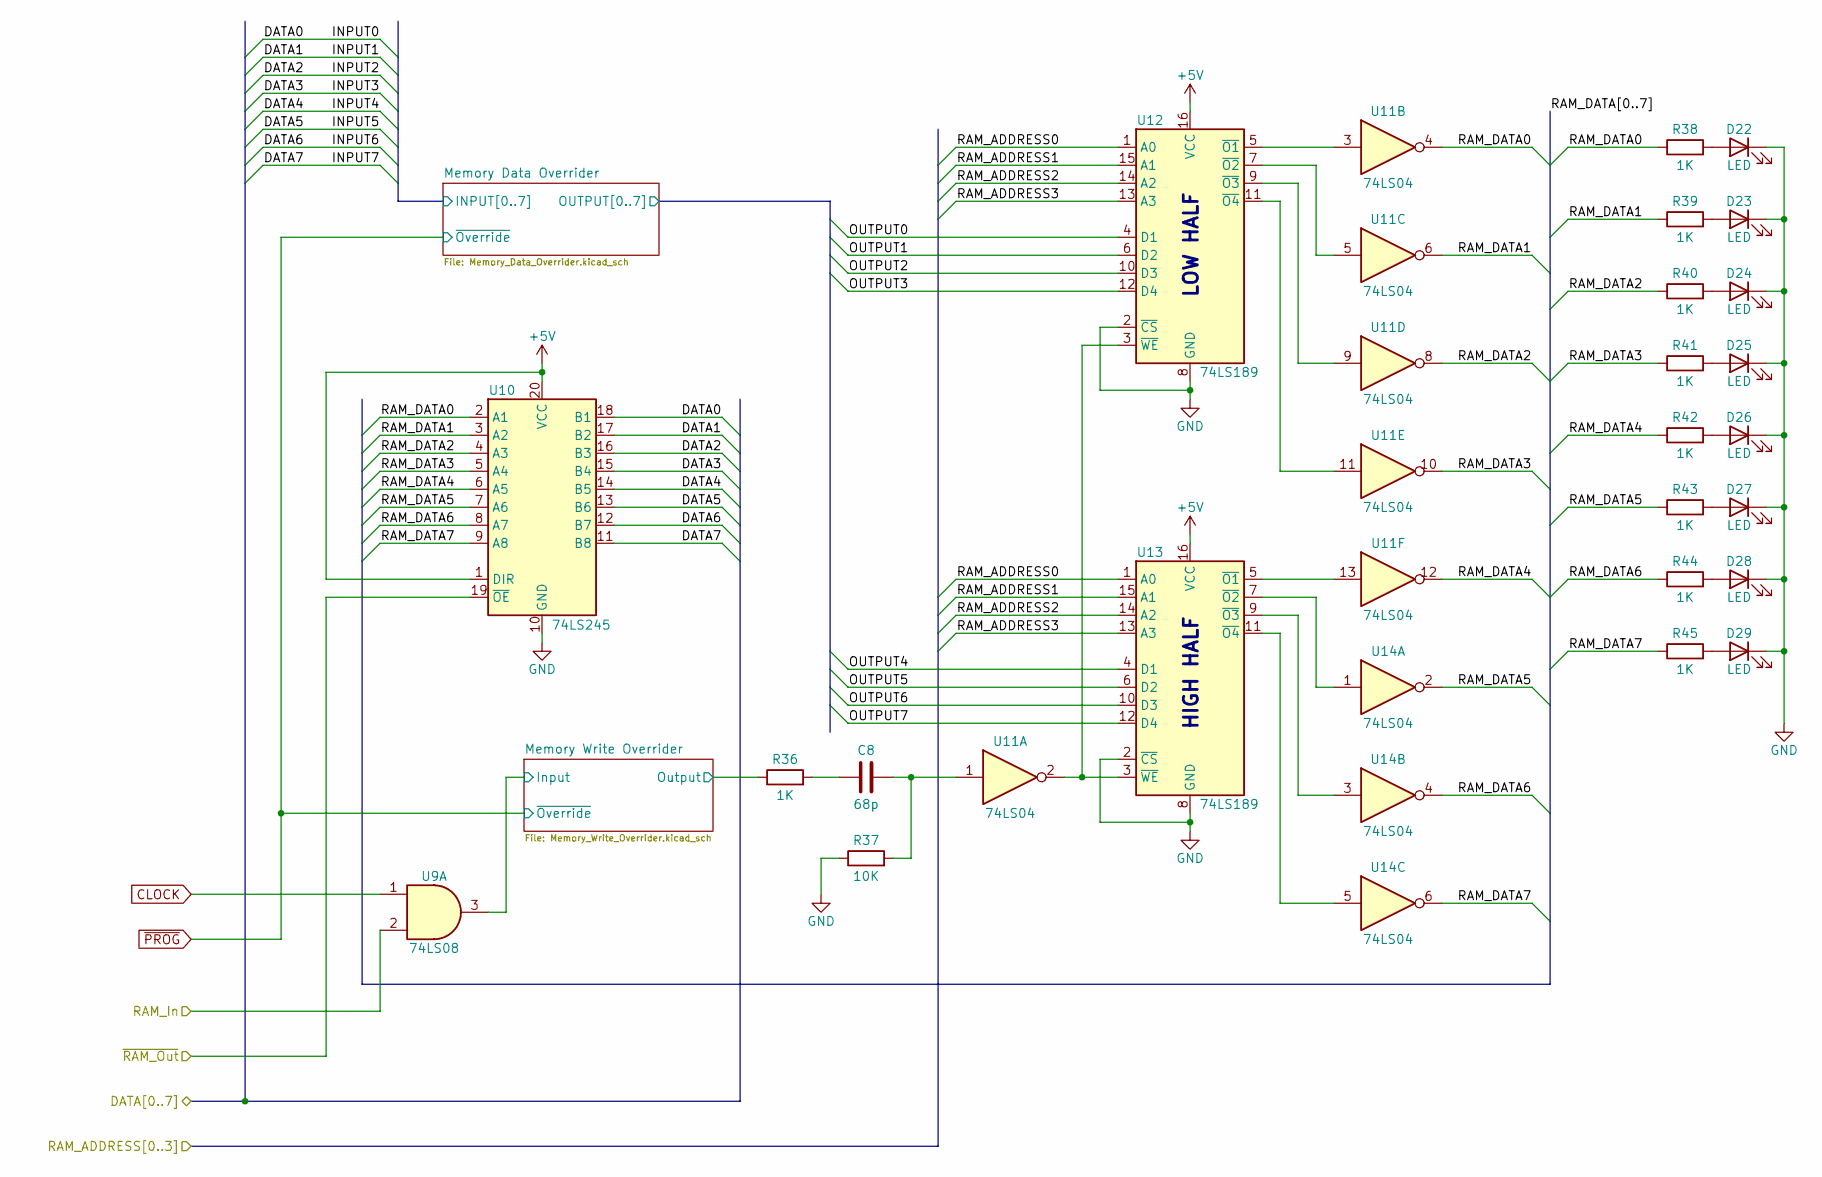
[picture p14: schematic RAM_Module.kicad_sch]

Parts:
C8: 68p; C_Disc_D5.1mm_W3.2mm_P5.00mm
D22, D23, D24, D25, D26, D27, D28, D29: LED; LED_D3.0mm
R36, R38, R39, R40, R41, R42, R43, R44, R45: 1K; R_Axial_DIN0207_L6.3mm_D2.5mm_P7.62mm_Horizontal
R37: 10K; R_Axial_DIN0207_L6.3mm_D2.5mm_P7.62mm_Horizontal
U9: 74LS08; DIP-14_W7.62mm
U10: 74LS245; DIP-20_W7.62mm
U11, U14: 74LS04; DIP-14_W7.62mm
U12, U13: 74LS189; DIP-16_W7.62mm

Connections:
+5V: U10.1 (DIR), U10.20 (VCC), U12.16 (VCC), U13.16 (VCC)
CLOCK: U9.1
DATA0: U10.18 (B1)
DATA1: U10.17 (B2)
DATA2: U10.16 (B3)
DATA3: U10.15 (B4)
DATA4: U10.14 (B5)
DATA5: U10.13 (B6)
DATA6: U10.12 (B7)
DATA7: U10.11 (B8)
GND: D22.1 (K), D23.1 (K), D24.1 (K), D25.1 (K), D26.1 (K), D27.1 (K), D28.1 (K), D29.1 (K), R37.1, U10.10 (GND), U12.2 (~CS), U12.8 (GND), U13.2 (~CS), U13.8 (GND)
Input: U9.3
unnamed: C8.1, R36.2
unnamed: C8.2, R37.2, U11.1
unnamed: D22.2 (A), R38.2
unnamed: D23.2 (A), R39.2
unnamed: D24.2 (A), R40.2
unnamed: D25.2 (A), R41.2
unnamed: D26.2 (A), R42.2
unnamed: D27.2 (A), R43.2
unnamed: D28.2 (A), R44.2
unnamed: D29.2 (A), R45.2
unnamed: U11.2, U12.3 (~WE), U13.3 (~WE)
unnamed: U11.3, U12.5 (~O1)
unnamed: U11.5, U12.7 (~O2)
unnamed: U11.9, U12.9 (~O3)
unnamed: U11.11, U12.11 (~O4)
unnamed: U11.13, U13.5 (~O1)
unnamed: U13.7 (~O2), U14.1
unnamed: U13.9 (~O3), U14.3
unnamed: U13.11 (~O4), U14.5
OUTPUT0: U12.4 (D1)
OUTPUT1: U12.6 (D2)
OUTPUT2: U12.10 (D3)
OUTPUT3: U12.12 (D4)
OUTPUT4: U13.4 (D1)
OUTPUT5: U13.6 (D2)
OUTPUT6: U13.10 (D3)
OUTPUT7: U13.12 (D4)
Output: R36.1
RAM_ADDRESS0: U12.1 (A0), U13.1 (A0)
RAM_ADDRESS1: U12.15 (A1), U13.15 (A1)
RAM_ADDRESS2: U12.14 (A2), U13.14 (A2)
RAM_ADDRESS3: U12.13 (A3), U13.13 (A3)
RAM_DATA0: R38.1, U10.2 (A1), U11.4
RAM_DATA1: R39.1, U10.3 (A2), U11.6
RAM_DATA2: R40.1, U10.4 (A3), U11.8
RAM_DATA3: R41.1, U10.5 (A4), U11.10
RAM_DATA4: R42.1, U10.6 (A5), U11.12
RAM_DATA5: R43.1, U10.7 (A6), U14.2
RAM_DATA6: R44.1, U10.8 (A7), U14.4
RAM_DATA7: R45.1, U10.9 (A8), U14.6
RAM_In: U9.2
~RAM_Out: U10.19 (~OE)

Notes on the sheet:
LOW HALF
HIGH HALF
