matanbright/8BitComputer/pcb-files/8-Bit_Computer/Register_A_Module.kicad_sch

## KiCad design pcb-files/8-Bit_Computer/Register_A_Module.kicad_sch (2024-03-10)

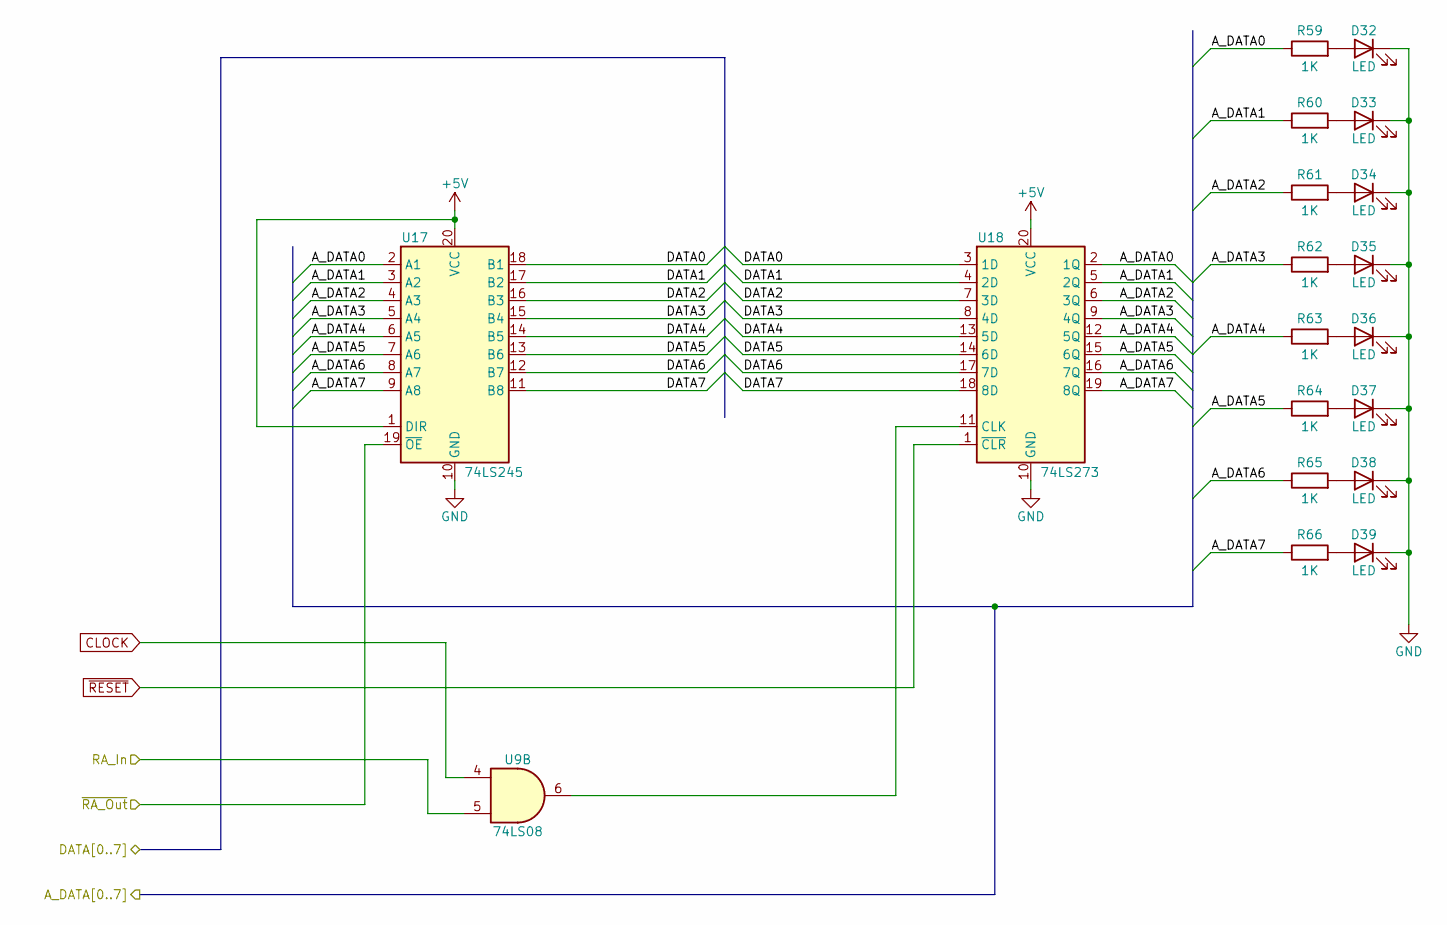
[picture p15: schematic Register_A_Module.kicad_sch]

Parts:
D32, D33, D34, D35, D36, D37, D38, D39: LED; LED_D3.0mm
R59, R60, R61, R62, R63, R64, R65, R66: 1K; R_Axial_DIN0207_L6.3mm_D2.5mm_P7.62mm_Horizontal
U9: 74LS08; DIP-14_W7.62mm
U17: 74LS245; DIP-20_W7.62mm
U18: 74LS273; DIP-20_W7.62mm

Connections:
+5V: U17.1 (DIR), U17.20 (VCC), U18.20 (VCC)
A_DATA0: R59.1, U17.2 (A1), U18.2 (1Q)
A_DATA1: R60.1, U17.3 (A2), U18.5 (2Q)
A_DATA2: R61.1, U17.4 (A3), U18.6 (3Q)
A_DATA3: R62.1, U17.5 (A4), U18.9 (4Q)
A_DATA4: R63.1, U17.6 (A5), U18.12 (5Q)
A_DATA5: R64.1, U17.7 (A6), U18.15 (6Q)
A_DATA6: R65.1, U17.8 (A7), U18.16 (7Q)
A_DATA7: R66.1, U17.9 (A8), U18.19 (8Q)
CLOCK: U9.4
DATA0: U17.18 (B1), U18.3 (1D)
DATA1: U17.17 (B2), U18.4 (2D)
DATA2: U17.16 (B3), U18.7 (3D)
DATA3: U17.15 (B4), U18.8 (4D)
DATA4: U17.14 (B5), U18.13 (5D)
DATA5: U17.13 (B6), U18.14 (6D)
DATA6: U17.12 (B7), U18.17 (7D)
DATA7: U17.11 (B8), U18.18 (8D)
GND: D32.1 (K), D33.1 (K), D34.1 (K), D35.1 (K), D36.1 (K), D37.1 (K), D38.1 (K), D39.1 (K), U17.10 (GND), U18.10 (GND)
unnamed: D32.2 (A), R59.2
unnamed: D33.2 (A), R60.2
unnamed: D34.2 (A), R61.2
unnamed: D35.2 (A), R62.2
unnamed: D36.2 (A), R63.2
unnamed: D37.2 (A), R64.2
unnamed: D38.2 (A), R65.2
unnamed: D39.2 (A), R66.2
unnamed: U9.6, U18.11 (CLK)
RA_In: U9.5
~RA_Out: U17.19 (~OE)
~RESET: U18.1 (~CLR)
