matanbright/8BitComputer/pcb-files/8-Bit_Computer/Register_B_Module.kicad_sch

## KiCad design pcb-files/8-Bit_Computer/Register_B_Module.kicad_sch (2024-03-10)

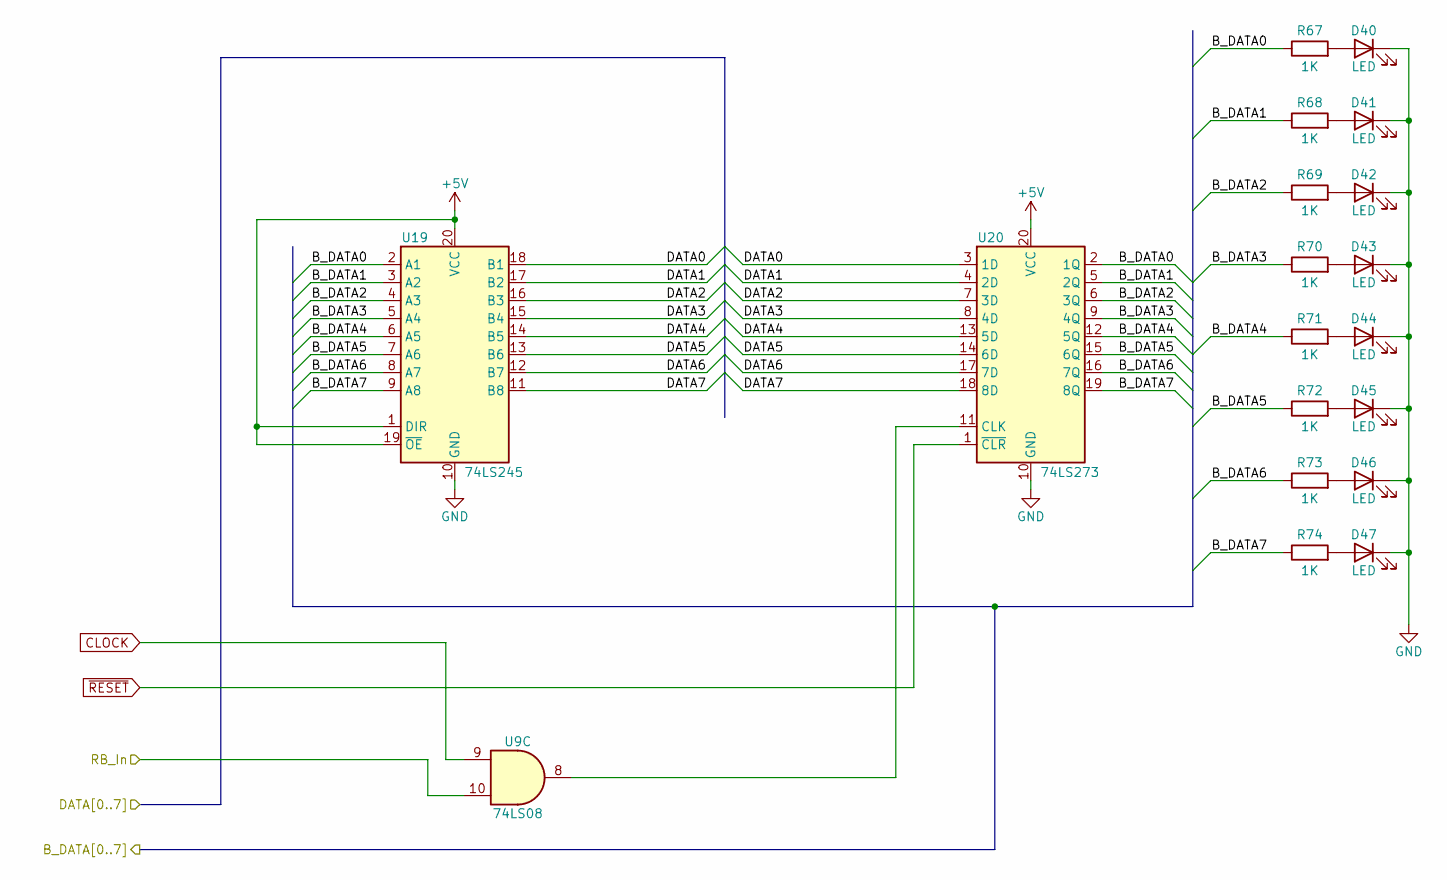
[picture p16: schematic Register_B_Module.kicad_sch]

Parts:
D40, D41, D42, D43, D44, D45, D46, D47: LED; LED_D3.0mm
R67, R68, R69, R70, R71, R72, R73, R74: 1K; R_Axial_DIN0207_L6.3mm_D2.5mm_P7.62mm_Horizontal
U9: 74LS08; DIP-14_W7.62mm
U19: 74LS245; DIP-20_W7.62mm
U20: 74LS273; DIP-20_W7.62mm

Connections:
+5V: U19.1 (DIR), U19.19 (~OE), U19.20 (VCC), U20.20 (VCC)
B_DATA0: R67.1, U19.2 (A1), U20.2 (1Q)
B_DATA1: R68.1, U19.3 (A2), U20.5 (2Q)
B_DATA2: R69.1, U19.4 (A3), U20.6 (3Q)
B_DATA3: R70.1, U19.5 (A4), U20.9 (4Q)
B_DATA4: R71.1, U19.6 (A5), U20.12 (5Q)
B_DATA5: R72.1, U19.7 (A6), U20.15 (6Q)
B_DATA6: R73.1, U19.8 (A7), U20.16 (7Q)
B_DATA7: R74.1, U19.9 (A8), U20.19 (8Q)
CLOCK: U9.9
DATA0: U19.18 (B1), U20.3 (1D)
DATA1: U19.17 (B2), U20.4 (2D)
DATA2: U19.16 (B3), U20.7 (3D)
DATA3: U19.15 (B4), U20.8 (4D)
DATA4: U19.14 (B5), U20.13 (5D)
DATA5: U19.13 (B6), U20.14 (6D)
DATA6: U19.12 (B7), U20.17 (7D)
DATA7: U19.11 (B8), U20.18 (8D)
GND: D40.1 (K), D41.1 (K), D42.1 (K), D43.1 (K), D44.1 (K), D45.1 (K), D46.1 (K), D47.1 (K), U19.10 (GND), U20.10 (GND)
unnamed: D40.2 (A), R67.2
unnamed: D41.2 (A), R68.2
unnamed: D42.2 (A), R69.2
unnamed: D43.2 (A), R70.2
unnamed: D44.2 (A), R71.2
unnamed: D45.2 (A), R72.2
unnamed: D46.2 (A), R73.2
unnamed: D47.2 (A), R74.2
unnamed: U9.8, U20.11 (CLK)
RB_In: U9.10
~RESET: U20.1 (~CLR)
